laszlodaniel/ChryslerScanner/PCB/V142/Assemblies/OBD2_female_connector_01.STEP

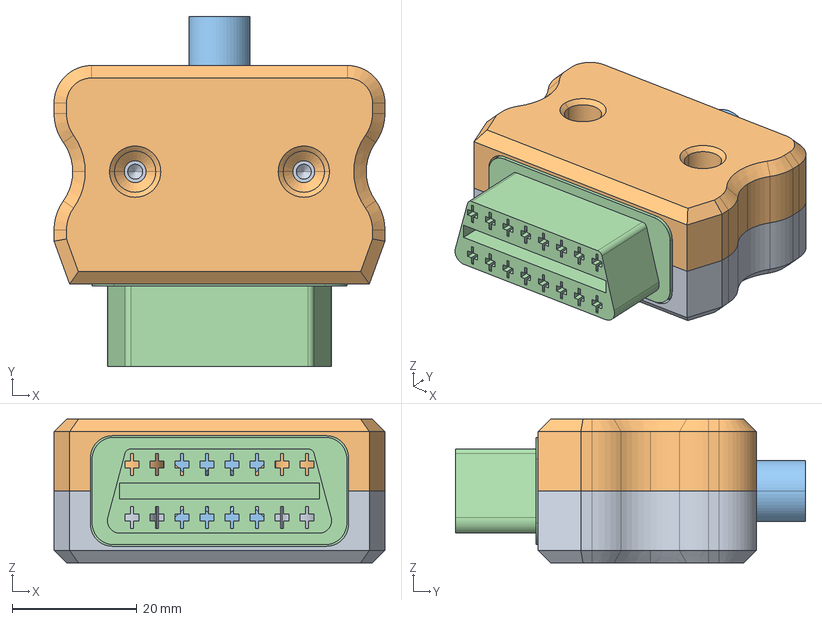
[picture p14: CAD file, 2019-10-13, an earlier design]
PCB/V142/Assemblies/OBD2_female_connector_01.STEP
53.0 x 56.1 x 23.0 mm
OBD2_connector_bottom_01
OBD2_connector_top_01
OBD2_cable_holder
SEP-A-OBD-D
