laszlodaniel/ChryslerScanner/PCB/V150/ChryslerCCDSCIScanner_V150/schematic/ChryslerCCDSCIScanner_V150_schematic_bw.pdf

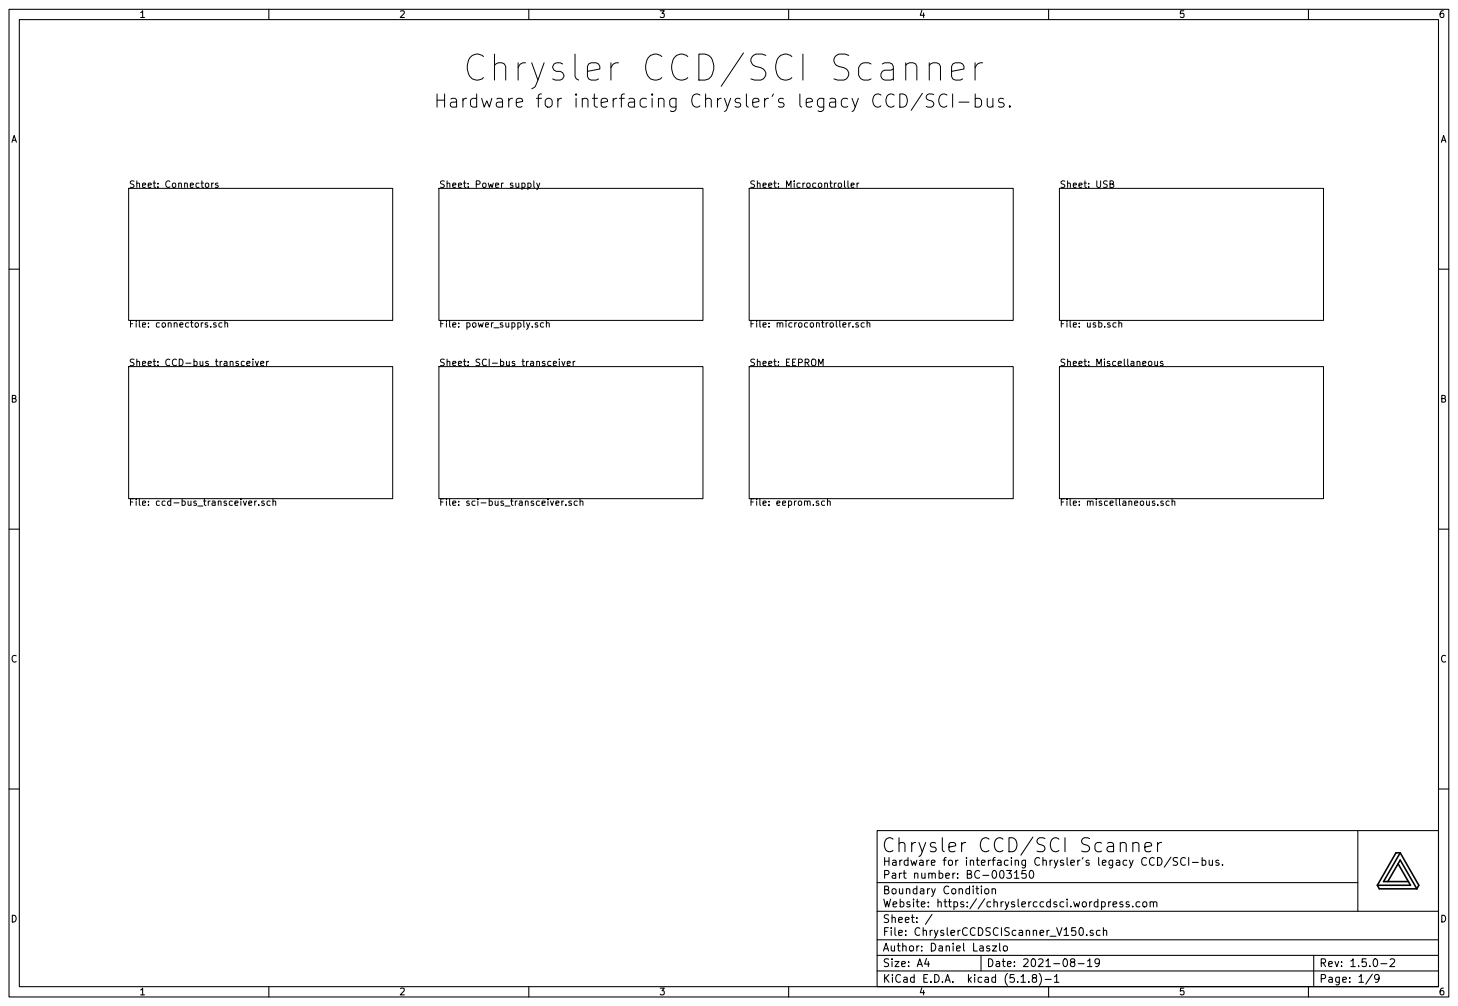
[picture p39: page 1]

Hardware for interfacing Chrysler's legacy CCD/SCI-bus.

Chrysler CCD/SCI Scanner
Part number: BC-003150 Hardware for interfacing Chrysler's legacy CCD/SCI-bus.

File: ChryslerCCDSCIScanner_V150.sch Sheet: / Boundary Condition Author: Daniel Laszlo Website: https://chryslerccdsci.wordpress.com

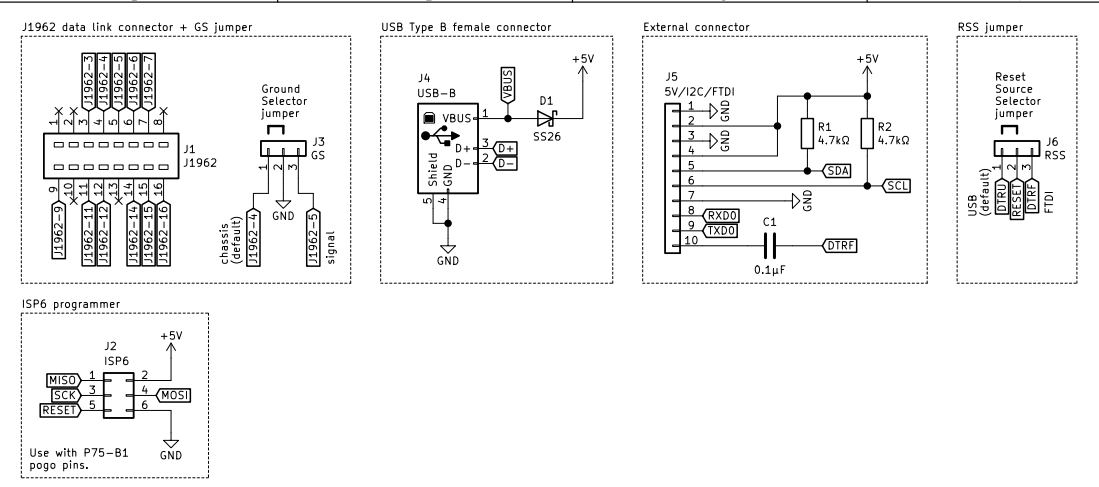
[picture p40: page 2]

Part number: BC-003150 Hardware for interfacing Chrysler's legacy CCD/SCI-bus. GND

Chrysler CCD/SCI Scanner File: connectors.sch Sheet: /Connectors/ Boundary Condition Author: Daniel Laszlo Website: https://chryslerccdsci.wordpress.com

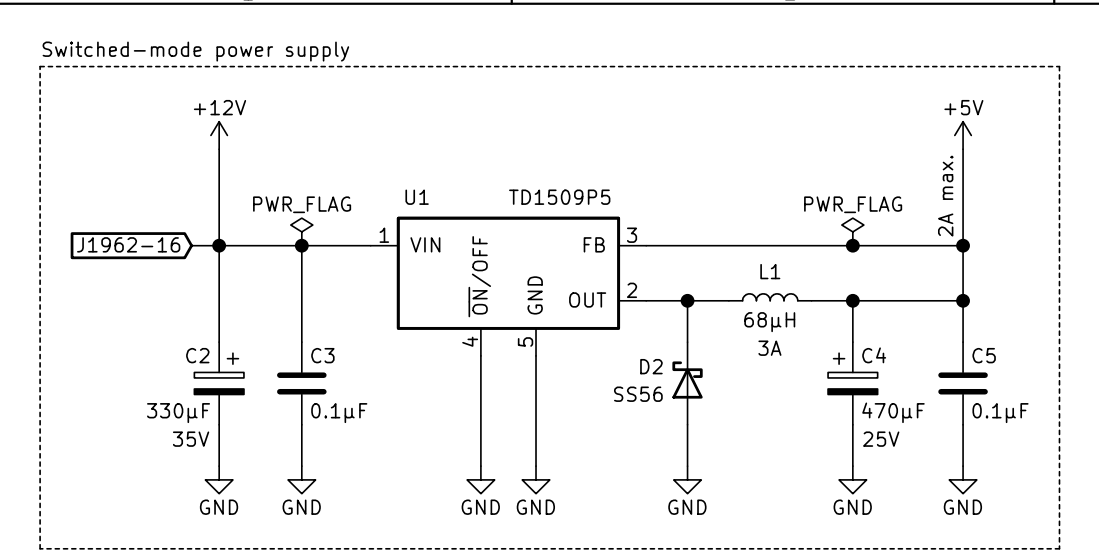
[picture p41: page 3]
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

Boundary Condition Author: Daniel Laszlo Website: https://chryslerccdsci.wordpress.com

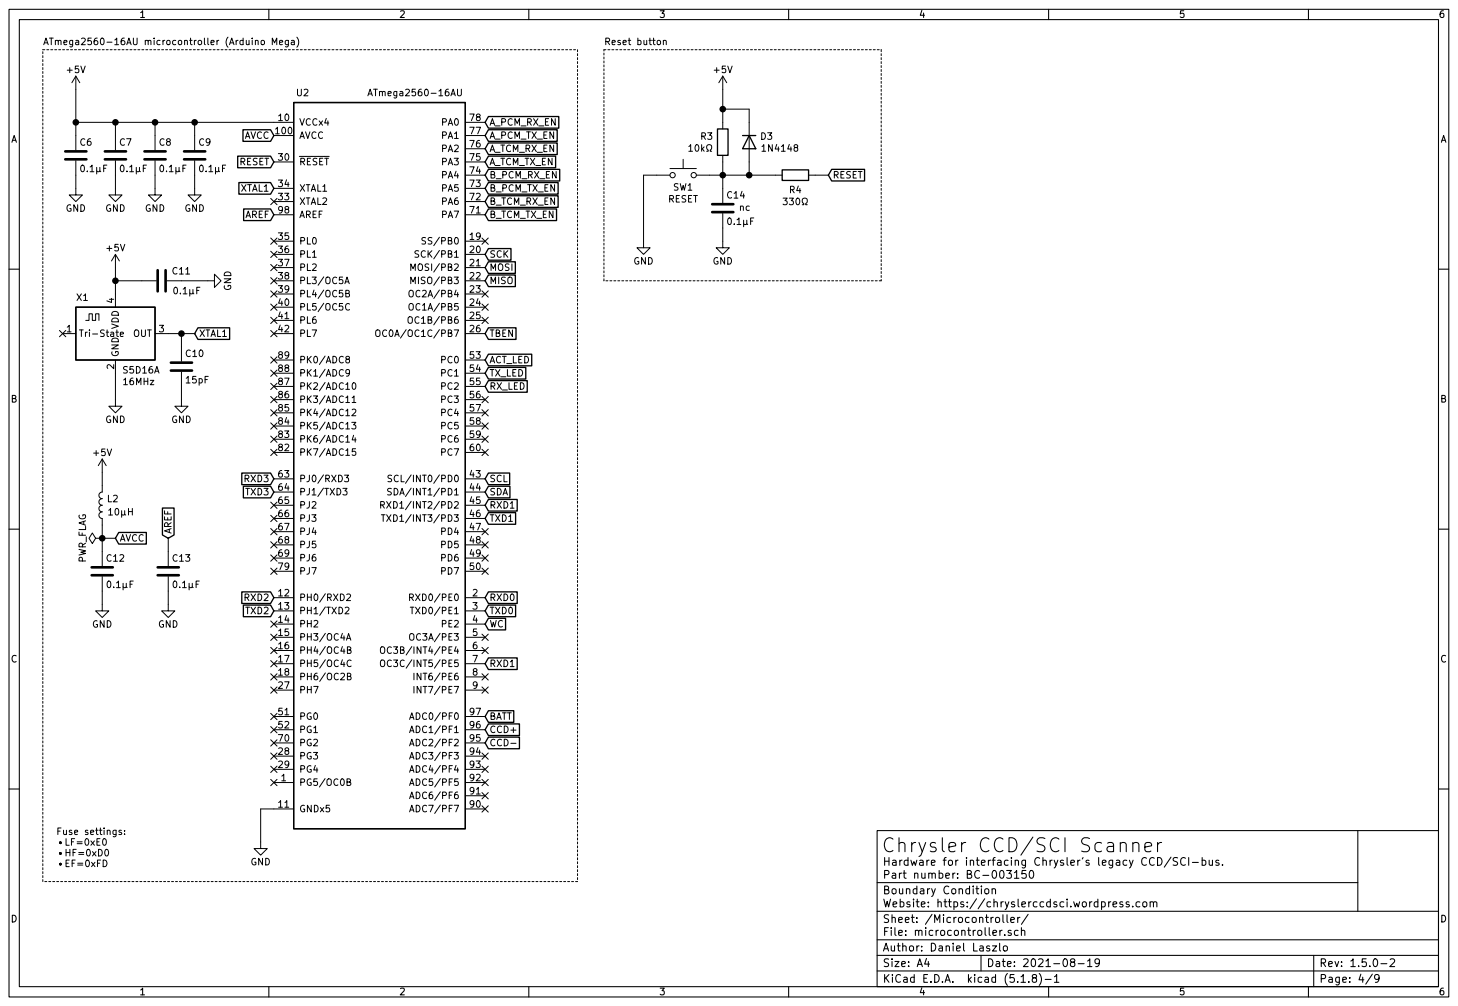
[picture p42: page 4]

Fuse settings: LF=0xE0 HF=0xD0 EF=0xFD

Chrysler CCD/SCI Scanner File: microcontroller.sch Sheet: /Microcontroller/ Boundary Condition Author: Daniel Laszlo Website: https://chryslerccdsci.wordpress.com

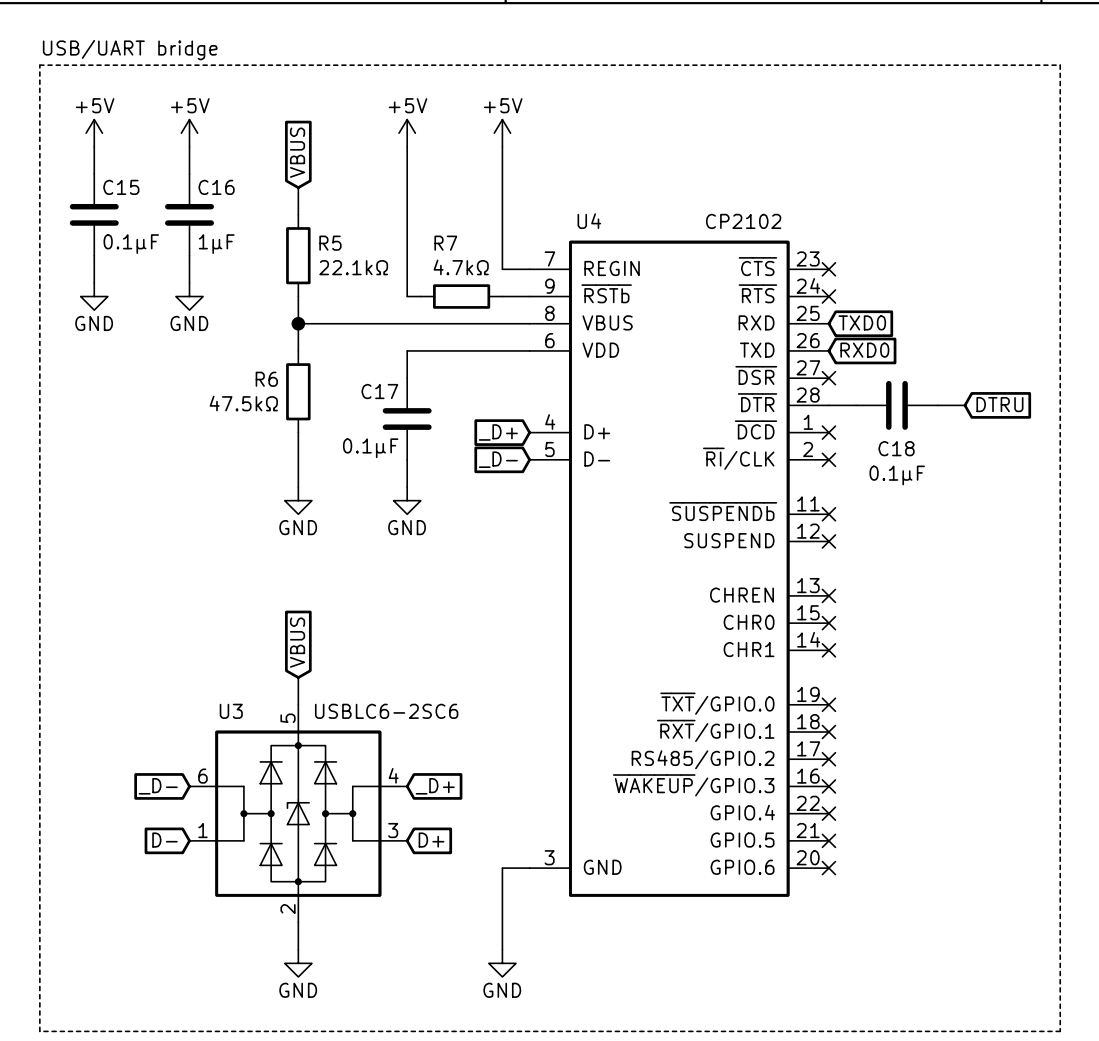
[picture p43: page 5]

Chrysler CCD/SCI Scanner File: usb.sch Sheet: /USB/ Boundary Condition Author: Daniel Laszlo Website: https://chryslerccdsci.wordpress.com
Part number: BC-003150 Hardware for interfacing Chrysler's legacy CCD/SCI-bus.

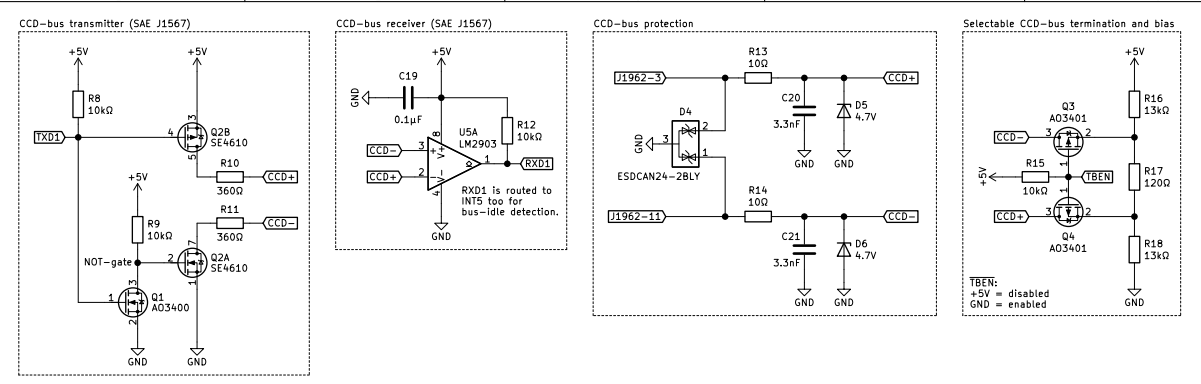
[picture p44: page 6]
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

File: ccd-bus_transceiver.sch Sheet: /CCD-bus transceiver/ Boundary Condition Author: Daniel Laszlo Website: https://chryslerccdsci.wordpress.com

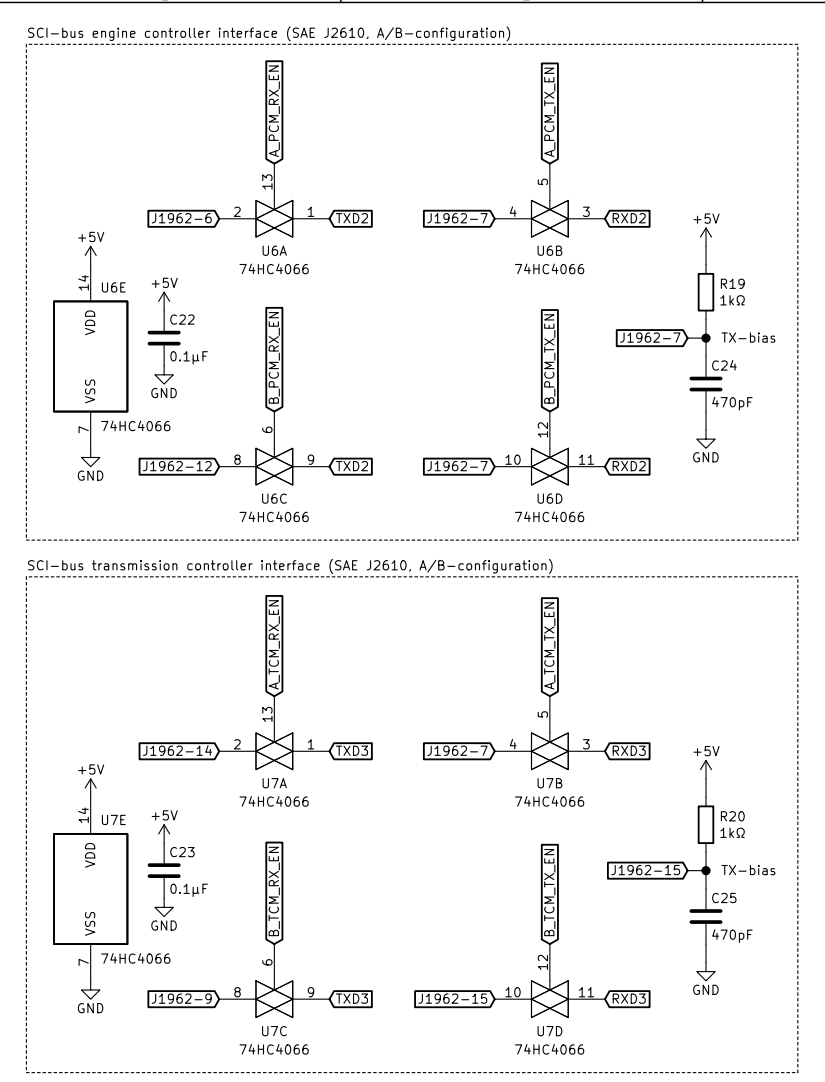
[picture p45: page 7]

Chrysler CCD/SCI Scanner

File: sci-bus_transceiver.sch Sheet: /SCI-bus transceiver/ Boundary Condition Author: Daniel Laszlo Website: https://chryslerccdsci.wordpress.com

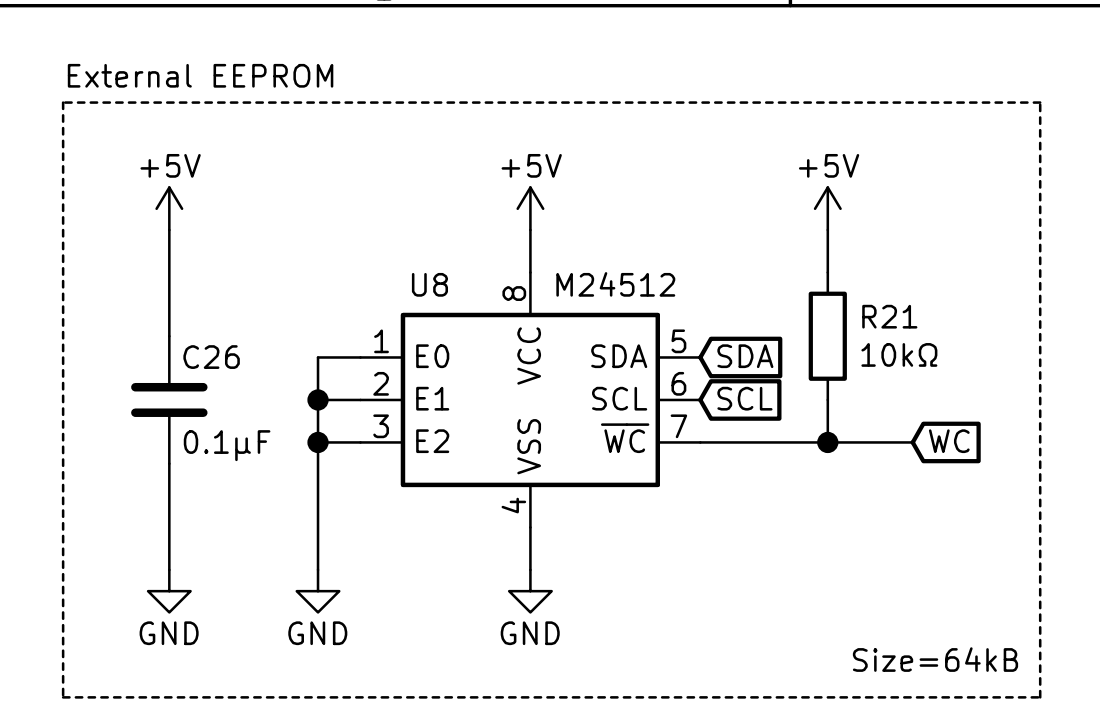
[picture p46: page 8]

4 SDA 5 SCL 6 WC 7 VCC

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

File: eeprom.sch Sheet: /EEPROM/ Boundary Condition Author: Daniel Laszlo Website: https://chryslerccdsci.wordpress.com

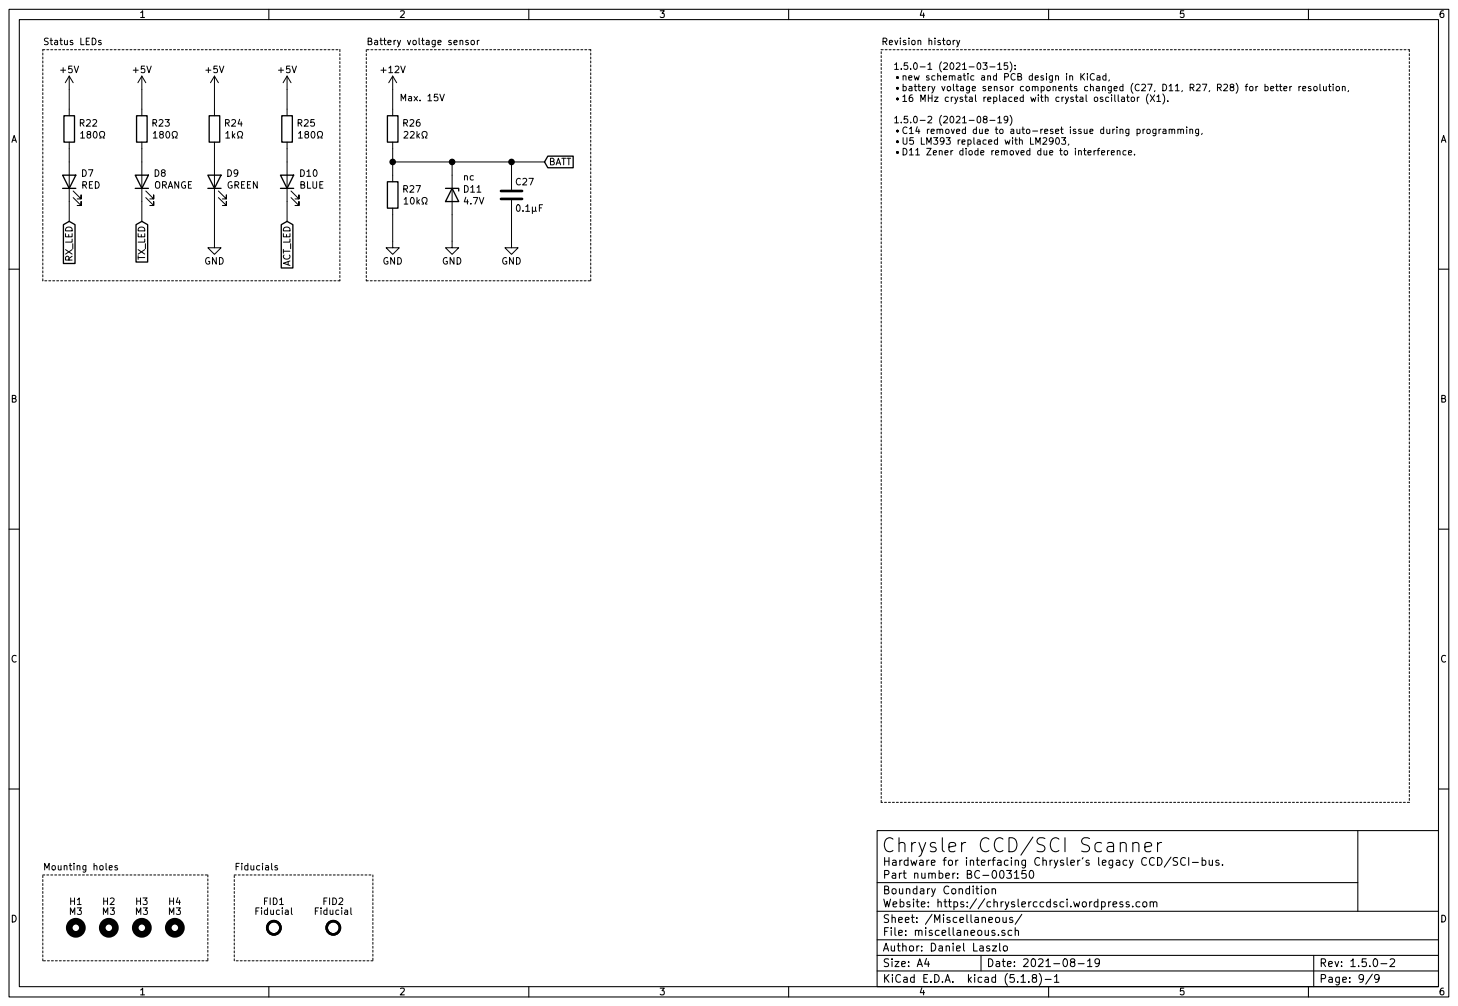
[picture p47: page 9]

new schematic and PCB design in KiCad,
battery voltage sensor components changed (C27, D11, R27, R28) for better resolution,
16 MHz crystal replaced with crystal oscillator (X1).

U5 LM393 replaced with LM2903, D11 Zener diode removed due to interference. Max. 15V Mounting holes

C14 removed due to auto-reset issue during programming,

Chrysler CCD/SCI Scanner File: miscellaneous.sch Sheet: /Miscellaneous/ Boundary Condition Author: Daniel Laszlo Website: https://chryslerccdsci.wordpress.com
Part number: BC-003150 Hardware for interfacing Chrysler's legacy CCD/SCI-bus.
