laszlodaniel/ChryslerScanner/PCB/V142/SCIBusLogicInverter_V100/schematic/SCIBusLogicInverter_V100_schematic.pdf

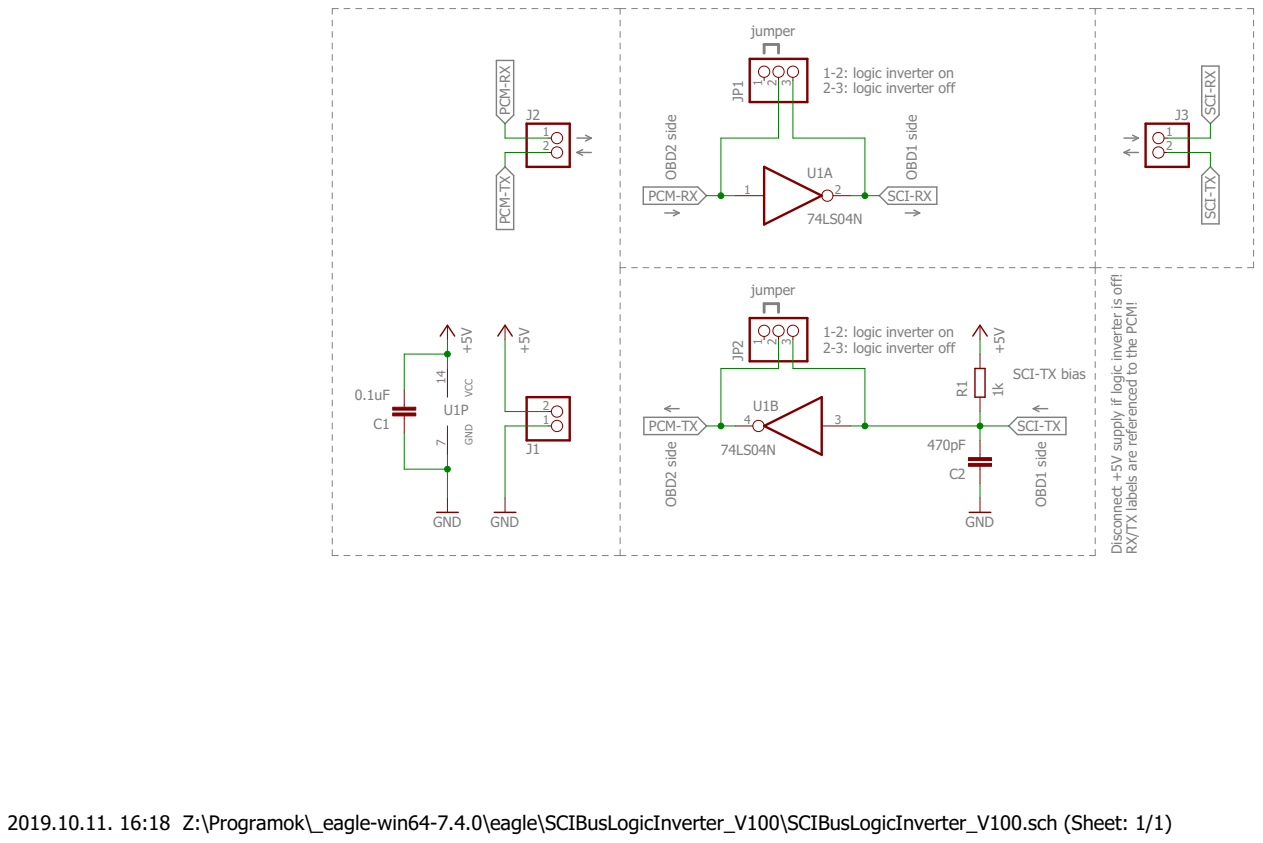
[picture p49: page 1]

SCI-TX SCI-RX

Disconnect +5V supply if logic inverter is of ! RX/TX labels are referenced to the PCM!

SCI-TX bias 1-2: logic inverter on
2-3: logic inverter off

2019.10.11. 16:18 Z:\Programok\_eagle-win64-7.4.0\eagle\SCIBusLogicInverter_V100\SCIBusLogicInverter_V100.sch (Sheet: 1/1)
