laszlodaniel/ChryslerScanner/PCB/V142/EngineConnector_V100/schematic/EngineConnector_V100_schematic.pdf

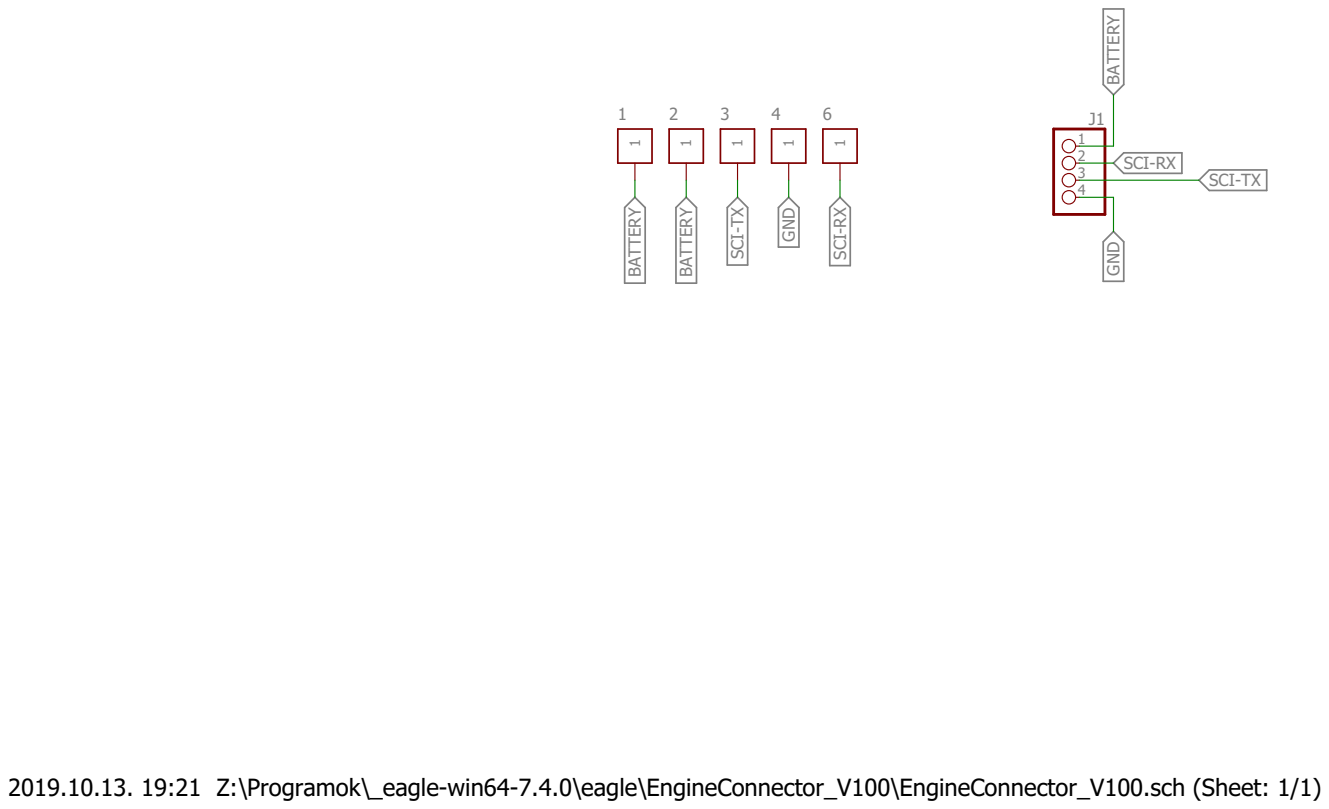
[picture p50: page 1]

2019.10.13. 19:21 Z:\Programok\_eagle-win64-7.4.0\eagle\EngineConnector_V100\EngineConnector_V100.sch (Sheet: 1/1)
