laszlodaniel/ChryslerScanner/Arduino/ChryslerCCDSCIScanner/ChryslerCCDSCIScanner.ino

/*
 * ChryslerCCDSCIScanner (https://github.com/laszlodaniel/ChryslerCCDSCIScanner)
 * Copyright (C) 2018-2023 Daniel Laszlo
 *
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
 * UART code is based on original library by Andy Gock:
 * https://github.com/andygock/avr-uart
 *
 * Board: Arduino/Genuino Mega or Mega 2560
 * Processor: ATmega2560 (Mega 2560)
 */

#include <avr/boot.h>
#include <avr/eeprom.h>
#include <avr/interrupt.h>
#include <avr/io.h>
#include <avr/pgmspace.h>
#include <avr/wdt.h>
#include <util/atomic.h>
#include <EEPROM.h>
#include <LiquidCrystal_I2C.h> // https://github.com/fdebrabander/Arduino-LiquidCrystal-I2C-library
#include <Wire.h>
#include <extEEPROM.h> // https://github.com/JChristensen/extEEPROM
#include <CCDLibrary.h> // https://github.com/laszlodaniel/CCDLibrary

// Firmware version (hexadecimal format):
// 00: major
// 09: minor
// 0C: patch
// (00: revision)
// = v0.9.12(.0)
#define FW_VERSION 0x00090C00

// Firmware date/time of compilation in 32-bit UNIX time:
// https://www.epochconverter.com/hex
// Upper 32 bits contain the firmware version.
#define FW_DATE 0x00090C006697BBA8

// Set (1), clear (0) and invert (1->0; 0->1) bit in a register or variable easily
//#define sbi(variable, bit) (variable) |=  (1 << (bit))
//#define cbi(variable, bit) (variable) &= ~(1 << (bit))
//#define ibi(variable, bit) (variable) ^=  (1 << (bit))

#define to_uint16(hb, lb)           (uint16_t)(((uint8_t)hb << 8) | (uint8_t)lb)
#define to_uint32(msb, hb, lb, lsb) (uint32_t)(((uint32_t)msb << 24) | ((uint32_t)hb << 16) | ((uint32_t)lb << 8) | (uint32_t)lsb)
#define ARRAY_SIZE(A) (sizeof(A) / sizeof((A)[0]))

#define USB_RX_BUFFER_SIZE 1024
#define USB_TX_BUFFER_SIZE 1024
#define USB_RX_BUFFER_MASK (USB_RX_BUFFER_SIZE - 1)
#define USB_TX_BUFFER_MASK (USB_TX_BUFFER_SIZE - 1)

#define USB_RECEIVE_INTERRUPT  USART0_RX_vect
#define USB_TRANSMIT_INTERRUPT USART0_UDRE_vect
#define USB_STATUS             UCSR0A
#define USB_CONTROL            UCSR0B
#define USB_DATA               UDR0
#define USB_UDRIE              UDRIE0

#define PCM_RX_BUFFER_SIZE 256
#define PCM_TX_BUFFER_SIZE 256
#define PCM_RX_BUFFER_MASK (PCM_RX_BUFFER_SIZE - 1)
#define PCM_TX_BUFFER_MASK (PCM_TX_BUFFER_SIZE - 1)

#define PCM_RECEIVE_INTERRUPT  USART2_RX_vect
#define PCM_TRANSMIT_INTERRUPT USART2_UDRE_vect
#define PCM_STATUS             UCSR2A
#define PCM_CONTROL            UCSR2B
#define PCM_DATA               UDR2
#define PCM_UDRIE              UDRIE2  

#define TCM_RX_BUFFER_SIZE 256
#define TCM_TX_BUFFER_SIZE 256
#define TCM_RX_BUFFER_MASK (TCM_RX_BUFFER_SIZE - 1)
#define TCM_TX_BUFFER_MASK (TCM_TX_BUFFER_SIZE - 1)

#define TCM_RECEIVE_INTERRUPT  USART3_RX_vect
#define TCM_TRANSMIT_INTERRUPT USART3_UDRE_vect
#define TCM_STATUS             UCSR3A
#define TCM_CONTROL            UCSR3B
#define TCM_DATA               UDR3
#define TCM_UDRIE              UDRIE3

#define BATT         A0 // battery voltage sensor analog input
#define CCD_POSITIVE A1 // CCD+ analog input
#define CCD_NEGATIVE A2 // CCD- analog input
#define TBEN         13 // CCD-bus termination and bias enable pin

#define A_PCM_RX_EN 22 // SCI-bus configuration selector digital pins on ATmega2560
#define A_PCM_TX_EN 23
#define A_TCM_RX_EN 24
#define A_TCM_TX_EN 25
#define B_PCM_RX_EN 26
#define B_PCM_TX_EN 27
#define B_TCM_RX_EN 28
#define B_TCM_TX_EN 29

#define RX_LED  35 // status LED (red), message received
#define TX_LED  36 // status LED (orange), message sent
#define ACT_LED 37 // status LED (blue), activity

// SAE J2610 (SCI-bus) recommended delays in milliseconds
#define SCI_LS_T1_DELAY 20
#define SCI_LS_T2_DELAY 100
#define SCI_LS_T3_DELAY 50
#define SCI_LS_T4_DELAY 20
#define SCI_LS_T5_DELAY 100
#define SCI_HS_T1_DELAY 1
#define SCI_HS_T2_DELAY 1
#define SCI_HS_T3_DELAY 5
#define SCI_HS_T4_DELAY 0
#define SCI_HS_T5_DELAY 0
#define SCI_BTSTRP_DLY  20

// SCI-bus setting bits
#define SCI_STATE_BIT         7
#define SCI_SBEC2_BIT         6
#define SCI_MODULE_BIT        5
#define SCI_NGC_BIT           4
#define SCI_LOGIC_BIT         3
#define SCI_CONFIG_BIT        2
#define SCI_SPEED_BITS        3
#define SCI_SPEED_BAUD_976    0
#define SCI_SPEED_BAUD_7812   1
#define SCI_SPEED_BAUD_62500  2
#define SCI_SPEED_BAUD_125000 3

// CCD-bus setting bits
#define CCD_STATE_BIT         7
#define CCD_TBEN_BIT          6

//#define UART_FRAME_ERROR        0x1000  /**< Framing Error by UART          00010000 00000000 - FIXED BIT */ 
//#define UART_OVERRUN_ERROR      0x0800  /**< Overrun condition by UART      00001000 00000000 - FIXED BIT */
//#define UART_BUFFER_OVERFLOW    0x0400  /**< Receive ringbuffer overflow    00000100 00000000 - ARBITRARY */
#define UART_RX_NO_DATA         0x0200  /**< Receive buffer is empty        00000010 00000000 - ARBITRARY */

// Baudrate prescaler calculation: UBRR = (F_CPU / (16 * BAUDRATE)) - 1
#define BAUD_976    1023 // prescaler for  976.5 baud speed (SCI-bus extra-low speed)
#define BAUD_7812   127  // prescaler for 7812.5 baud speed (CCD/SCI-bus default low-speed diagnostic mode)
#define BAUD_62500  15   // prescaler for  62500 baud speed (SCI-bus high-speed parameter mode)
#define BAUD_125000 7    // prescaler for 125000 baud speed (SCI-bus extra-high speed)
#define BAUD_250000 3    // prescaler for 250000 baud speed (USB communication)

#define PACKET_SYNC_BYTE   0x3D // "=" symbol
#define ASCII_SYNC_BYTE    0x3E // ">" symbol
#define MAX_PAYLOAD_LENGTH USB_RX_BUFFER_SIZE - 6  // 1024-6 bytes
#define EMPTY_PAYLOAD      0xFE  // Random byte, could be anything

#define BUFFER_SIZE 256

// DATA CODE byte building blocks
// Bus masks (high nibble (3 bits))
#define bus_usb             0x00 // when sending packets back to laptop use "from_" masks to specify source
#define bus_ccd             0x01
#define bus_pcm             0x02
#define bus_tcm             0x03
// Commands (low nibble (4 bits))
#define reset               0x00
#define handshake           0x01
#define status              0x02
#define settings            0x03
#define request             0x04
#define response            0x05
#define msg_tx              0x06
#define msg_rx              0x07
// 0x08-0x0D reserved
#define debug               0x0E
#define ok_error            0x0F

// SUB-DATA CODE byte
// Command 0x00 (reset)
#define reset_in_progress   0x00
#define reset_done          0x01
// 0x02-0xFF reserved

// SUB-DATA CODE byte
// Command 0x01 (handshake)
// 0x00-0xFF reserved

// SUB-DATA CODE byte
// Command 0x02 (status)
// 0x00-0xFF reserved

// SUB-DATA CODE byte
// Command 0x03 (settings)
#define heartbeat           0x01 // ACT_LED flashing interval is stored in payload
#define set_ccd_bus         0x02 // ON-OFF state is stored in payload
#define set_sci_bus         0x03 // ON-OFF state, A/B configuration and speed are stored in payload
#define set_repeat_behavior 0x04 // Repeated message behavior settings
#define set_lcd             0x05 // ON-OFF state
// 0x06-0xFF reserved 

// SUB-DATA CODE byte
// Command 0x04 & 0x05 (request and response)
#define hwfw_info           0x01 // Hardware version/date and firmware date in this particular order (dates are in 64-bit UNIX time format)
#define timestamp           0x02 // elapsed milliseconds since system start
#define battery_voltage     0x03 // flag for battery voltage packet
#define exteeprom_checksum  0x04
#define ccd_bus_voltages    0x05
// 0x06-0xFF reserved

// SUB-DATA CODE byte
// Command 0x06 (msg_tx)
#define stop_msg_flow       0x01 // stop message transmission (single and repeated as well)         
#define single_msg          0x02 // send message to the target bus specified in DATA CODE byte; message is stored in payload 
#define list_msg            0x03 // send a set of messages to the target bus specified in DATA CODE byte; messages are stored in payload
#define repeated_single_msg 0x04 // send message(s) repeatedly to the target bus sepcified in DATA CODE byte
#define repeated_list_msg   0x05 // send a fixed set of messages repeatedly to the target bus specified in DATA CODE byte
// 0x06-0xFF reserved

// SUB-DATA CODE byte
// Command 0x07 (msg_rx)
#define sci_ls_bytes        0x01 // low-speed SCI-bus message
#define sci_hs_bytes        0x02 // high-speed SCI-bus message
// 0x03-0xFF reserved

// SUB-DATA CODE byte
// Command 0x0E (debug)
#define random_ccd_msg            0x01
#define read_inteeprom_byte       0x02
#define read_inteeprom_block      0x03
#define read_exteeprom_byte       0x04
#define read_exteeprom_block      0x05
#define write_inteeprom_byte      0x06
#define write_inteeprom_block     0x07
#define write_exteeprom_byte      0x08
#define write_exteeprom_block     0x09
#define set_arbitrary_uart_speed  0x0A
#define init_bootstrap_mode       0x0B
#define upload_worker_function    0x0C
#define start_worker_function     0x0D
#define exit_worker_function      0x0E
#define restore_pcm_eeprom        0xF0

// SUB-DATA CODE byte
// Command 0x0F (ok_error)
#define ok                                      0x00
#define error_length_invalid_value              0x01
#define error_datacode_invalid_command          0x02
#define error_subdatacode_invalid_value         0x03
#define error_payload_invalid_values            0x04
#define error_packet_checksum_invalid_value     0x05
#define error_packet_timeout_occurred           0x06
#define error_buffer_overflow                   0x07
#define error_datacode_invalid_bus              0x08
// 0x09-0xF6 reserved
#define error_sci_ls_no_response                0xF6
#define error_not_enough_mcu_ram                0xF7
#define error_sci_hs_memory_ptr_no_response     0xF8
#define error_sci_hs_invalid_memory_ptr         0xF9
#define error_sci_hs_no_response                0xFA
#define error_eep_not_found                     0xFB
#define error_eep_read                          0xFC
#define error_eep_write                         0xFD
#define error_internal                          0xFE
#define error_fatal                             0xFF

#define STOP  0x00
#define START 0x01

uint8_t ack[1] = { 0x00 }; // acknowledge payload array
uint8_t err[1] = { 0xFF }; // error payload array

uint8_t avr_signature[3];
uint8_t hw_version[2];
uint8_t hw_date[8];
uint8_t assembly_date[8];

uint32_t current_millis = 0;
uint8_t current_timestamp[4]; // current time is stored here when "update_timestamp" is called

uint8_t command_timeout = 100; // milliseconds
uint16_t command_purge_timeout = 200; // milliseconds, if a command isn't complete within this time then delete the usb receive buffer

typedef struct {
    bool enabled = false; // bus state (enabled or disabled)
    bool termination_bias_enabled = false;
    bool inverted_logic = false; // OBD1 SCI engine adapter cable needs special message handling
    bool sbec2_mode = false; // OBD1 reverse bit order inside byte
    bool ngc_mode = false; // NGC computers use full-duplex SCI-bus communication
    uint8_t bus_settings = 0;
    uint16_t speed = BAUD_7812; // baudrate prescaler - 1023: 976.5625 baud; 127: 7812.5 baud; 15: 62500 baud; 7: 125000 baud; 3: 250000 baud
    volatile bool idle = true; // bus idling (CCD-bus only, IDLE-pin)
    volatile bool busy = false; // there's a byte being transmitted on the bus (CCD-bus only, CTRL-pin)
    bool echo_received = false; // low-speed mode (7812.5 baud)
    bool response_received = false; // low-speed mode (7812.5 baud) typical 1-byte response flag
    uint8_t message[32];
    uint16_t message_length = 0;
    uint8_t msg_buffer[BUFFER_SIZE]; // temporary buffer to store outgoing or current repeated messages
    uint16_t msg_buffer_ptr = 0; // message length in the buffer, this points to the first empty slot after the last byte
    uint8_t msg_to_transmit_count = 0;
    uint8_t msg_to_transmit_count_ptr = 0;
    volatile uint32_t last_byte_millis = 0;
    bool msg_tx_pending = false; // message is awaiting to be transmitted to the bus
    bool repeat = false;
    bool repeat_next = false;
    bool repeat_list_once = false;
    bool repeat_stop = true;
    uint16_t repeated_msg_length = 0;
    uint32_t repeated_msg_raw_start = 0; // iteration start, 4-bytes max
    uint32_t repeated_msg_raw_end = 0; // iteration end, 4-bytes max
    uint16_t repeated_msg_increment = 1; // if iteration is true then the counter in the message will increase this much for every new message
    uint16_t repeated_msg_interval = 100; // ms
    uint32_t repeated_msg_last_millis = 0;
    uint8_t repeat_retry_counter = 0;
    bool random_msg = false;
    uint16_t random_msg_interval = 0;
    uint16_t random_msg_interval_min = 0;
    uint16_t random_msg_interval_max = 0;
    uint32_t random_msg_last_millis = 0;
    volatile uint32_t msg_rx_count = 0; // total received messages
    volatile uint32_t msg_tx_count = 0; // total transmitted messages
    uint8_t last_hs_memarea = 0xF4;
    uint8_t auto_request = 0;
} bus_t;

bus_t ccd, pcm, tcm;

// Construct an object called "eep" for the external 24LC32A EEPROM chip.
extEEPROM eep(kbits_32, 1, 32, 0x50); // device size: 32 kilobits = 4 kilobytes, number of devices: 1, page size: 32 bytes (from datasheet), device address: 0x50 by default

bool eep_present = false;
uint8_t eep_status = 0; // extEEPROM connection status is stored here
uint8_t eep_result = 0; // extEEPROM 

// Construct an object called "lcd" for the external display.
LiquidCrystal_I2C lcd(0x27, 20, 4);

bool lcd_enabled = false;
uint8_t lcd_i2c_address = 0;
uint8_t lcd_char_width = 0;
uint8_t lcd_char_height = 0;
uint8_t lcd_refresh_rate = 0;
uint8_t lcd_units = 0; // 0-imperial, 1-metric
uint8_t lcd_data_source = 1; // 1: CCD-bus, 2: SCI-bus (PCM), 3: SCI-bus (TCM)
uint32_t lcd_last_update = 0;
uint16_t lcd_update_interval = 0;
bool lcd_splash_screen_on = true;

// Custom LCD-characters
// https://maxpromer.github.io/LCD-Character-Creator/
uint8_t up_symbol[8]     = { 0x00, 0x04, 0x0E, 0x15, 0x04, 0x04, 0x00, 0x00 }; // ↑
uint8_t down_symbol[8]   = { 0x00, 0x04, 0x04, 0x15, 0x0E, 0x04, 0x00, 0x00 }; // ↓
uint8_t left_symbol[8]   = { 0x00, 0x04, 0x08, 0x1F, 0x08, 0x04, 0x00, 0x00 }; // ←
uint8_t right_symbol[8]  = { 0x00, 0x04, 0x02, 0x1F, 0x02, 0x04, 0x00, 0x00 }; // →
uint8_t enter_symbol[8]  = { 0x00, 0x01, 0x05, 0x09, 0x1F, 0x08, 0x04, 0x00 }; // 
uint8_t degree_symbol[8] = { 0x06, 0x09, 0x09, 0x06, 0x00, 0x00, 0x00, 0x00 }; // °

char vin_characters[] = "-----------------"; // 17 characters
String vin_string;

volatile uint8_t  USB_RxBuf[USB_RX_BUFFER_SIZE];
volatile uint8_t  USB_TxBuf[USB_TX_BUFFER_SIZE];
volatile uint16_t USB_RxHead; // since buffer size is bigger than 256 bytes it has to be a 16-bit (int) variable
volatile uint16_t USB_RxTail;
volatile uint16_t USB_TxHead;
volatile uint16_t USB_TxTail;
volatile uint8_t  USB_LastRxError;

volatile uint8_t PCM_RxBuf[PCM_RX_BUFFER_SIZE];
volatile uint8_t PCM_TxBuf[PCM_TX_BUFFER_SIZE];
volatile uint8_t PCM_RxHead;
volatile uint8_t PCM_RxTail;
volatile uint8_t PCM_TxHead;
volatile uint8_t PCM_TxTail;
volatile uint8_t PCM_LastRxError;

volatile uint8_t TCM_RxBuf[TCM_RX_BUFFER_SIZE];
volatile uint8_t TCM_TxBuf[TCM_TX_BUFFER_SIZE];
volatile uint8_t TCM_RxHead;
volatile uint8_t TCM_RxTail;
volatile uint8_t TCM_TxHead;
volatile uint8_t TCM_TxTail;
volatile uint8_t TCM_LastRxError;

uint8_t sci_hi_speed_memarea[16] = { 0xF0, 0xF1, 0xF2, 0xF3, 0xF4, 0xF5, 0xF6, 0xF7, 0xF8, 0xF9, 0xFA, 0xFB, 0xFC, 0xFD, 0xFE, 0xFF };
uint8_t sci_lo_speed_cmd_filter[6] = { 0x14, 0x15, 0x26, 0x27, 0x28, 0x2A };

uint32_t ccd_positive_adc = 0;   // raw analog reading is stored here
uint16_t ccd_positive_volts = 0; // converted to CCD+ voltage and multiplied by 100: 2.51V -> 251
uint32_t ccd_negative_adc = 0;   // raw analog reading is stored here
uint16_t ccd_negative_volts = 0; // converted to CCD- voltage and multiplied by 100: 2.51V -> 251
uint8_t ccd_volts_array[4]; // ccd_positive_volts and ccd_negative_volts is separated to byte components here

uint32_t previous_random_ccd_msg_millis = 0;

uint16_t adc_supply_voltage = 500; // supply voltage multiplied by 100: 5.00V -> 500
uint16_t rd_high_value = 27000; // high resistor value in the divider (R19): 27 kOhm = 27000
uint16_t rd_low_value = 5000;  // low resistor value in the divider (R20): 5 kOhm = 5000
uint16_t adc_max_value = 1023; // 1023 for 10-bit resolution
uint32_t battery_adc = 0;   // raw analog reading is stored here
uint16_t battery_volts = 0; // converted to battery voltage and multiplied by 100: 12.85V -> 1285
uint8_t battery_volts_array[2]; // battery_volts is separated to byte components here
bool connected_to_vehicle = false;

uint32_t rx_led_ontime = 0;
uint32_t tx_led_ontime = 0;
uint32_t act_led_ontime = 0;
uint32_t previous_act_blink = 0;
uint16_t led_blink_duration = 50; // milliseconds
uint16_t heartbeat_interval = 5000; // milliseconds
bool heartbeat_enabled = true;

// Bootloaders:

// SBEC3 (128k).
const uint8_t LdBoot_128k_SBEC3[516] PROGMEM =
{
    0x37, 0x80, 0x00, 0xac, 0xfa, 0x00, 0x01, 0x98, 0xf8, 0x10, 0xb7, 0x02, 0xf8, 0x20, 0xb7, 0x58, 
    0xb6, 0xee, 0xf5, 0x11, 0xfa, 0x00, 0x01, 0x82, 0xfa, 0x00, 0x01, 0x98, 0x17, 0xfa, 0x01, 0xb0, 
    0x17, 0xf5, 0x01, 0xb0, 0xfa, 0x00, 0x01, 0x82, 0xfa, 0x00, 0x01, 0x98, 0x17, 0xfa, 0x01, 0xb1, 
    0x17, 0xf5, 0x01, 0xb1, 0xfa, 0x00, 0x01, 0x82, 0xf5, 0x00, 0x37, 0x9c, 0x37, 0xbc, 0x02, 0x00, 
    0xfa, 0x00, 0x01, 0x98, 0xca, 0x00, 0xc5, 0x00, 0xfa, 0x00, 0x01, 0x82, 0x3c, 0x01, 0x27, 0x31, 
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
    0x37, 0xfc, 0xf5, 0xa5, 0x27, 0xf7, 0x17, 0x65, 0x7c, 0x0c, 0x76, 0x01, 0xb7, 0xf4, 0x17, 0xea, 
    0x7c, 0x0f, 0x27, 0xf7, 0x17, 0x65, 0x7c, 0x0d, 0x76, 0x42, 0x78, 0x40, 0xb6, 0xf2, 0x17, 0xe5, 
    0x7c, 0x0f, 0x27, 0xf7, 0x37, 0xb0, 0x00, 0x01, 0xb6, 0xf6, 0x27, 0xf7, 0x27, 0x4c, 0x27, 0x4c, 
    0x27, 0x4c, 0x27, 0x4c
};

// Empty.
const uint8_t LdWorker_empty_SBEC3[2] =
{
    0x27, 0xf7
};

/*************************************************************************
Function: solve_sbec3_bootstrap_seed()
Purpose:  solve the bootstrap security challenge
Note:     provided by Konstantin aka Piton
**************************************************************************/
uint16_t solve_sbec3_bootstrap_seed(uint16_t input)
{
    uint16_t seed = (input + 0x247C) | 5;
    int i = seed & 0x0F;

    while (i--)
    {
        if (seed & 1) seed = ((seed >> 1) | 0x8000);
        else seed >>= 1;
    }

    return (seed | 0x247C);
}

uint16_t pcm_peek(uint16_t index = 0); // function prototype

/*************************************************************************
Function: unlock_bootstrap_mode()
Purpose:  solve the bootstrap security seed and upload bootloader
**************************************************************************/
void unlock_sbec3_bootstrap_mode(uint8_t bootloader_src)
{
    uint8_t ret[1] = { 0 };
    // 0 = ok
    // 1 = no response to magic byte
    // 2 = unexpected response to magic byte
    // 3 = security seed response timeout
    // 4 = security seed response checksum error
    // 5 = security key status timeout
    // 6 = security key not accepted
    // 7 = start bootloader timeout
    // 8 = unexpected bootloader status byte

    uint8_t buff[16];
    uint8_t checksum = 0;
    bool key_required = true;

    wdt_reset(); // feed the watchdog
    pcm_rx_flush();
    pcm_tx_flush();
    pcm.last_byte_millis = millis();

    // Write magic byte to set 62500 baud.
    pcm_putc(0x7F);

    while ((uint32_t)(millis() - pcm.last_byte_millis) < SCI_BTSTRP_DLY); // wait for response

    if (pcm_rx_available() == 0)
    {
        ret[0] = 1;
        send_usb_packet(bus_usb, debug, init_bootstrap_mode, ret, 1);
        pcm_rx_flush();
        return;
    }

    buff[0] = pcm_getc() & 0xFF;

    if (buff[0] != 0x06)
    {
        ret[0] = 2;
        send_usb_packet(bus_usb, debug, init_bootstrap_mode, ret, 1);
        pcm_rx_flush();
        return;
    }

    uint8_t req_seed_cmd[5] = { 0x24, 0xD0, 0x27, 0xC1, 0xDC };

    wdt_reset(); // feed the watchdog
    pcm_rx_flush();
    pcm.last_byte_millis = millis();

    // Write security seed request message.
    for (uint8_t i = 0; i < ARRAY_SIZE(req_seed_cmd); i++)
    {
        pcm_putc(req_seed_cmd[i]);
    }

    while ((uint32_t)(millis() - pcm.last_byte_millis) < (2 * SCI_BTSTRP_DLY)); // wait for response

    if (pcm_rx_available() < 7)
    {
        if ((pcm_rx_available() == 5) && (pcm_peek(0) == 0xDB) && (pcm_peek(1) == 0x2F) && (pcm_peek(2) == 0xD8) && (pcm_peek(3) == 0x3E) && (pcm_peek(4) == 0x23))
        {
            key_required = false;
        }
        else
        {
            ret[0] = 3;
            send_usb_packet(bus_usb, debug, init_bootstrap_mode, ret, 1);
            pcm_rx_flush();
            return;
        }
    }

    if (key_required)
    {
        // Read security seed response.
        for (uint8_t i = 0; i < 7; i++)
        {
            buff[i] = pcm_getc() & 0xFF;
    
            if (i < 6) checksum += buff[i]; // calculate checksum
        }

        uint8_t key[2];

        // Evaluate seed response message and solve the puzzle.
        if ((buff[0] == 0x26) && (buff[1] == 0xD0) && (buff[2] == 0x67) && (buff[3] == 0xC1) && (buff[6] == checksum))
        {
            uint16_t data = solve_sbec3_bootstrap_seed(to_uint16(buff[4], buff[5]));
            key[0] = (data >> 8) & 0xFF;
            key[1] = data & 0xFF;
        }
        else
        {
            ret[0] = 4;
            send_usb_packet(bus_usb, debug, init_bootstrap_mode, ret, 1);
            pcm_rx_flush();
            return;
        }

        uint8_t send_key_cmd[7] = { 0x24, 0xD0, 0x27, 0xC2, key[0], key[1], 0 };
        send_key_cmd[6] = calculate_checksum(send_key_cmd, 0, ARRAY_SIZE(send_key_cmd) - 1);

        wdt_reset(); // feed the watchdog
        pcm_rx_flush();
        pcm.last_byte_millis = millis();

        // Write security key message.
        for (uint8_t i = 0; i < ARRAY_SIZE(send_key_cmd); i++)
        {
            pcm_putc(send_key_cmd[i]);
        }

        while ((uint32_t)(millis() - pcm.last_byte_millis) < (2 * SCI_BTSTRP_DLY)); // wait for response

        if (pcm_rx_available() < 5)
        {
            ret[0] = 5;
            send_usb_packet(bus_usb, debug, init_bootstrap_mode, ret, 1);
            pcm_rx_flush();
            return;
        }

        // Read security key status.
        for (uint8_t i = 0; i < 5; i++)
        {
            buff[i] = pcm_getc() & 0xFF;
        }

        // Key not accepted.
        if (!((buff[0] == 0x26) && (buff[1] == 0xD0) && (buff[2] == 0x67) && (buff[3] == 0xC2) && (buff[4] == 0x1F)))
        {
            ret[0] = 6;
            send_usb_packet(bus_usb, debug, init_bootstrap_mode, ret, 1);
            pcm_rx_flush();
            return;
        }
    }

    wdt_reset(); // feed the watchdog
    pcm_rx_flush();

    // Upload bootloader.
    switch (bootloader_src)
    {
        case 1: // SBEC3 (128k)
        {
            uint8_t bl_header[5] = { 0x4C, 0x01, 0x00, (((0x0100 + ARRAY_SIZE(LdBoot_128k_SBEC3) - 1) >> 8) & 0xFF), ((0x0100 + ARRAY_SIZE(LdBoot_128k_SBEC3) - 1) & 0xFF) };

            for (uint8_t i = 0; i < ARRAY_SIZE(bl_header); i++)
            {
                pcm_putc(bl_header[i]);
                while (pcm_rx_available() == 0); // wait for echo
                pcm_getc(); // read echo into oblivion
            }
            
            for (uint16_t i = 0; i < ARRAY_SIZE(LdBoot_128k_SBEC3); i++)
            {
                pcm_putc(pgm_read_byte(LdBoot_128k_SBEC3 + i));
                while (pcm_rx_available() == 0); // wait for echo
                pcm_getc(); // read echo into oblivion
            }
            break;
        }
        case 2: // SBEC3 (256k)
        {
            uint8_t bl_header[5] = { 0x4C, 0x01, 0x00, (((0x0100 + ARRAY_SIZE(LdBoot_256k_SBEC3) - 1) >> 8) & 0xFF), ((0x0100 + ARRAY_SIZE(LdBoot_256k_SBEC3) - 1) & 0xFF) };

            for (uint8_t i = 0; i < ARRAY_SIZE(bl_header); i++)
            {
                pcm_putc(bl_header[i]);
                while (pcm_rx_available() == 0); // wait for echo
                pcm_getc(); // read echo into oblivion
            }

            for (uint16_t i = 0; i < ARRAY_SIZE(LdBoot_256k_SBEC3); i++)
            {
                pcm_putc(pgm_read_byte(LdBoot_256k_SBEC3 + i));
                while (pcm_rx_available() == 0); // wait for echo
                pcm_getc(); // read echo into oblivion
            }
            break;
        }
        case 3: // SBEC3 256k custom by Dino
        {
            uint8_t bl_header[5] = { 0x4C, 0x01, 0x00, (((0x0100 + ARRAY_SIZE(LdBoot_256k_SBEC3_custom) - 1) >> 8) & 0xFF), ((0x0100 + ARRAY_SIZE(LdBoot_256k_SBEC3_custom) - 1) & 0xFF) };

            for (uint8_t i = 0; i < ARRAY_SIZE(bl_header); i++)
            {
                pcm_putc(bl_header[i]);
                while (pcm_rx_available() == 0); // wait for echo
                pcm_getc(); // read echo into oblivion
            }

            for (uint16_t i = 0; i < ARRAY_SIZE(LdBoot_256k_SBEC3_custom); i++)
            {
                pcm_putc(pgm_read_byte(LdBoot_256k_SBEC3_custom + i));
                while (pcm_rx_available() == 0); // wait for echo
                pcm_getc(); // read echo into oblivion
            }
            break;
        }
        case 0:
        default:
        {
            uint8_t bl_header[5] = { 0x4C, 0x01, 0x00, (((0x0100 + ARRAY_SIZE(LdBoot_empty_SBEC3) - 1) >> 8) & 0xFF), ((0x0100 + ARRAY_SIZE(LdBoot_empty_SBEC3) - 1) & 0xFF) };

            for (uint8_t i = 0; i < ARRAY_SIZE(bl_header); i++)
            {
                pcm_putc(bl_header[i]);
                while (pcm_rx_available() == 0); // wait for echo
                pcm_getc(); // read echo into oblivion
            }

            for (uint16_t i = 0; i < ARRAY_SIZE(LdBoot_empty_SBEC3); i++)
            {
                pcm_putc(pgm_read_byte(LdBoot_empty_SBEC3 + i));
                while (pcm_rx_available() == 0); // wait for echo
                pcm_getc(); // read echo into oblivion
            }
            break;
        }
    }

    wdt_reset(); // feed the watchdog
    pcm_rx_flush();

    uint8_t start_bootloader_cmd[3] = { 0x47, 0x01, 0x00 };

    // Write start bootloader message.
    for (uint8_t i = 0; i < ARRAY_SIZE(start_bootloader_cmd); i++)
    {
        pcm_putc(start_bootloader_cmd[i]);
        while (pcm_rx_available() == 0); // wait for echo
        pcm_getc(); // read echo into oblivion
    }

    while ((uint32_t)(millis() - pcm.last_byte_millis) < SCI_BTSTRP_DLY); // wait for response

    if (pcm_rx_available() == 0)
    {
        ret[0] = 7;
        send_usb_packet(bus_usb, debug, init_bootstrap_mode, ret, 1);
        pcm_rx_flush();
        return;
    }

    uint8_t bootloader_status = pcm_getc() & 0xFF;

    if (bootloader_status != 0x22)
    {
        ret[0] = 8;
        send_usb_packet(bus_usb, debug, init_bootstrap_mode, ret, 1);
        pcm_rx_flush();
        return;
    }

    wdt_reset(); // feed the watchdog
    pcm_rx_flush();

    // Success.
    send_usb_packet(bus_usb, debug, init_bootstrap_mode, ret, 1);
}

/*************************************************************************
Function: upload_worker_function()
Purpose:  upload worker function in bootstrap mode
**************************************************************************/
void write_worker_function(uint8_t worker_function_src)
{
    uint8_t ret[1] = { 0 };
    // 0 = ok
    // 1 = upload interrupted
    // 2 = unexpected upload result
    // 3 = function did not start
    // 4 = unexpected function start status

    wdt_reset(); // feed the watchdog
    pcm_rx_flush();
    
    switch (worker_function_src)
    {
        case 1: // part number read
        {
            uint8_t wf_header[3] = { 0x10, ((ARRAY_SIZE(LdPartNumberRead_SBEC3) >> 8) & 0xFF), (ARRAY_SIZE(LdPartNumberRead_SBEC3) & 0xFF) };

            for (uint8_t i = 0; i < ARRAY_SIZE(wf_header); i++)
            {
                pcm_putc(wf_header[i]);
                while (pcm_rx_available() == 0); // wait for echo
                pcm_getc(); // read echo into oblivion
            }

            for (uint16_t i = 0; i < ARRAY_SIZE(LdPartNumberRead_SBEC3); i++)
            {
                pcm_putc(pgm_read_byte(LdPartNumberRead_SBEC3 + i));
                while (pcm_rx_available() == 0); // wait for echo
                pcm_getc(); // read echo into oblivion
            }
            break;
        }
        case 2: // flash manufacturer and chip ID read
        {
            uint8_t wf_header[3] = { 0x10, ((ARRAY_SIZE(LdFlashID_SBEC3) >> 8) & 0xFF), (ARRAY_SIZE(LdFlashID_SBEC3) & 0xFF) };

            for (uint8_t i = 0; i < ARRAY_SIZE(wf_header); i++)
            {
                pcm_putc(wf_header[i]);
                while (pcm_rx_available() == 0); // wait for echo
                pcm_getc(); // read echo into oblivion
            }

            for (uint16_t i = 0; i < ARRAY_SIZE(LdFlashID_SBEC3); i++)
            {
                pcm_putc(pgm_read_byte(LdFlashID_SBEC3 + i));
                while (pcm_rx_available() == 0); // wait for echo
                pcm_getc(); // read echo into oblivion
            }
            break;
        }
        case 3: // flash read
        {
            uint8_t wf_header[3] = { 0x10, ((ARRAY_SIZE(LdFlashRead_SBEC3) >> 8) & 0xFF), (ARRAY_SIZE(LdFlashRead_SBEC3) & 0xFF) };

            for (uint8_t i = 0; i < ARRAY_SIZE(wf_header); i++)
            {
                pcm_putc(wf_header[i]);
                while (pcm_rx_available() == 0); // wait for echo
                pcm_getc(); // read echo into oblivion
            }

            for (uint16_t i = 0; i < ARRAY_SIZE(LdFlashRead_SBEC3); i++)
            {
                pcm_putc(pgm_read_byte(LdFlashRead_SBEC3 + i));
                while (pcm_rx_available() == 0); // wait for echo
                pcm_getc(); // read echo into oblivion
            }
            break;
        }
        case 7: // EEPROM read
        {
            uint8_t wf_header[3] = { 0x10, ((ARRAY_SIZE(LdEEPROMRead_SBEC3) >> 8) & 0xFF), (ARRAY_SIZE(LdEEPROMRead_SBEC3) & 0xFF) };

            for (uint8_t i = 0; i < ARRAY_SIZE(wf_header); i++)
            {
                pcm_putc(wf_header[i]);
                while (pcm_rx_available() == 0); // wait for echo
                pcm_getc(); // read echo into oblivion
            }

            for (uint16_t i = 0; i < ARRAY_SIZE(LdEEPROMRead_SBEC3); i++)
            {
                pcm_putc(pgm_read_byte(LdEEPROMRead_SBEC3 + i));
                while (pcm_rx_available() == 0); // wait for echo
                pcm_getc(); // read echo into oblivion
            }
            break;
        }
        case 8: // EEPROM write
        {
            uint8_t wf_header[3] = { 0x10, ((ARRAY_SIZE(LdEEPROMWrite_SBEC3) >> 8) & 0xFF), (ARRAY_SIZE(LdEEPROMWrite_SBEC3) & 0xFF) };

            for (uint8_t i = 0; i < ARRAY_SIZE(wf_header); i++)
            {
                pcm_putc(wf_header[i]);
                while (pcm_rx_available() == 0); // wait for echo
                pcm_getc(); // read echo into oblivion
            }

            for (uint16_t i = 0; i < ARRAY_SIZE(LdEEPROMWrite_SBEC3); i++)
            {
                pcm_putc(pgm_read_byte(LdEEPROMWrite_SBEC3 + i));
                while (pcm_rx_available() == 0); // wait for echo
                pcm_getc(); // read echo into oblivion
            }
            break;
        }
        case 0:
        default:
        {
            uint8_t wf_header[3] = { 0x10, ((ARRAY_SIZE(LdWorker_empty_SBEC3) >> 8) & 0xFF), (ARRAY_SIZE(LdWorker_empty_SBEC3) & 0xFF) };

            for (uint8_t i = 0; i < ARRAY_SIZE(wf_header); i++)
            {
                pcm_putc(wf_header[i]);
                while (pcm_rx_available() == 0); // wait for echo
                pcm_getc(); // read echo into oblivion
            }

            for (uint16_t i = 0; i < ARRAY_SIZE(LdWorker_empty_SBEC3); i++)
            {
                pcm_putc(pgm_read_byte(LdWorker_empty_SBEC3 + i));
                while (pcm_rx_available() == 0); // wait for echo
                pcm_getc(); // read echo into oblivion
            }
            break;
            break;
        }
    }

    // Wait for upload finished status byte.
    while ((uint32_t)(millis() - pcm.last_byte_millis) < SCI_BTSTRP_DLY); // wait for response

    if (pcm_rx_available() == 0)
    {
        ret[0] = 1;
        send_usb_packet(bus_usb, debug, upload_worker_function, ret, 1);
        pcm_rx_flush();
        return;
    }

    uint8_t upload_status = pcm_getc() & 0xFF;

    if (upload_status != 0x14)
    {
        ret[0] = 2;
        send_usb_packet(bus_usb, debug, upload_worker_function, ret, 1);
        pcm_rx_flush();
        return;
    }

//    wdt_reset(); // feed the watchdog
//    pcm_rx_flush();
//    pcm.last_byte_millis = millis();
//
//    // Start worker function.
//    pcm_putc(0x20);
//
//    while ((uint32_t)(millis() - pcm.last_byte_millis) < SCI_BTSTRP_DLY); // wait for response
//
//    if (pcm_rx_available() == 0)
//    {
//        ret[0] = 3;
//        send_usb_packet(bus_usb, debug, upload_worker_function, ret, 1);
//        pcm_rx_flush();
//        return;
//    }
//
//    uint8_t start_status = pcm_getc() & 0xFF;
//
//    if (start_status != 0x21)
//    {
//        ret[0] = 4;
//        send_usb_packet(bus_usb, debug, upload_worker_function, ret, 1);
//        pcm_rx_flush();
//        return;
//    }

    wdt_reset(); // feed the watchdog
    pcm_rx_flush();

    // Success.
    send_usb_packet(bus_usb, debug, upload_worker_function, ret, 1);
}

/*************************************************************************
Function: restore_pcm_eeprom_handler()
Purpose:  read current PCM EEPROM value and replace with backup value if different
**************************************************************************/
void restore_pcm_eeprom_handler(uint8_t *input_data)
{
    uint8_t ret[1] = { 0 };
    // 0 = ok
    // 1 = no response to security seed request
    // 2 = checksum error
    // 3 = no response to key
    // 4 = key not accepted
    // 5 = read EEPROM command not returning a value
    // 6 = write EEPROM command not returning a result
    // 7 = write EEPROM command failed

    wdt_reset(); // feed the watchdog
    pcm_rx_flush();
    pcm_tx_flush();
    pcm.last_byte_millis = millis();

    // Get security seed challenge.
    pcm_putc(0x2B);

    while ((pcm_rx_available() < 4) && ((uint32_t)(millis() - pcm.last_byte_millis) < 200)); // wait for response

    if (pcm_rx_available() < 4)
    {
        ret[0] = 1;
        send_usb_packet(bus_usb, debug, restore_pcm_eeprom, ret, 1);
        pcm_rx_flush();
        return;
    }

    uint8_t buff[16];
    uint8_t buff_ptr = 0;
    uint8_t checksum = 0;

    for (uint8_t i = 0; i < 4; i++)
    {
        buff[i] = pcm_getc() & 0xFF;

        if (i < 3) checksum += buff[i]; // calculate checksum
    }

    if (buff[3] != checksum)
    {
        ret[0] = 2;
        send_usb_packet(bus_usb, debug, restore_pcm_eeprom, ret, 1);
        pcm_rx_flush();
        return;
    }

    send_usb_packet(bus_pcm, msg_rx, sci_ls_bytes, buff, 4);

    bool key_required = true;

    if ((buff[1] == 0) && (buff[2] == 0))
    {
        key_required = false;
    }

    if (key_required)
    {
        uint16_t seed = to_uint16(buff[1], buff[2]);
        uint16_t a = (seed << 2) + 0x9018;
        uint8_t key[2] = { ((a >> 8) & 0xFF), (a & 0xFF) };

        uint8_t send_key_cmd[4] = { 0x2C, key[0], key[1], 0 };
        send_key_cmd[3] = calculate_checksum(send_key_cmd, 0, ARRAY_SIZE(send_key_cmd) - 1);

        wdt_reset(); // feed the watchdog
        pcm_rx_flush();
        buff_ptr = 0;

        // Write security key message.
        for (uint8_t i = 0; i < ARRAY_SIZE(send_key_cmd); i++)
        {
            pcm_putc(send_key_cmd[i]);
            while (pcm_rx_available() == 0); // wait for echo
            buff[i] = pcm_getc() & 0xFF; // read echo into buffer
            buff_ptr++;
        }

        while ((pcm_rx_available() == 0) && (uint32_t)(millis() - pcm.last_byte_millis) < 200); // wait for response

        if (pcm_rx_available() == 0)
        {
            ret[0] = 3;
            send_usb_packet(bus_usb, debug, restore_pcm_eeprom, ret, 1);
            pcm_rx_flush();
            return;
        }

        // Read key status.
        buff[buff_ptr] = pcm_getc() & 0xFF;
        buff_ptr++;

        send_usb_packet(bus_pcm, msg_rx, sci_ls_bytes, buff, buff_ptr);

        if (buff[4] != 0)
        {
            ret[0] = 4;
            send_usb_packet(bus_usb, debug, restore_pcm_eeprom, ret, 1);
            pcm_rx_flush();
            return;
        }
    }

    wdt_reset(); // feed the watchdog
    pcm_rx_flush();

    uint8_t read_eeprom_cmd[3] = { 0x28, 0x00, 0x00 };
    uint8_t write_eeprom_cmd[4] = { 0x27, 0x00, 0x00, 0x00 };
    uint8_t offset[2] = { 0, 0 };
    uint8_t attempts = 0;
    bool valid_response = false;

    for (uint16_t i = 0; i < 512; i++) // EEPROM size = 512 bytes
    {
        // Set current offset.
        offset[0] = (i >> 8) & 0xFF;
        offset[1] = i & 0xFF;
        read_eeprom_cmd[1] = offset[0];
        read_eeprom_cmd[2] = offset[1];

        valid_response = false;
        attempts = 0;

        while (!valid_response)
        {
            wdt_reset(); // feed the watchdog
            pcm_rx_flush();
            buff_ptr = 0;

            // Read current EEPROM value.
            for (uint8_t j = 0; j < ARRAY_SIZE(read_eeprom_cmd); j++)
            {
                pcm_putc(read_eeprom_cmd[j]);
                while (pcm_rx_available() == 0); // wait for echo
                buff[j] = pcm_getc() & 0xFF; // read echo into buffer
                buff_ptr++;
            }

            while ((pcm_rx_available() == 0) && ((uint32_t)(millis() - pcm.last_byte_millis) < 300)); // wait for response

            if (pcm_rx_available() == 0)
            {
                attempts++;

                if (attempts >= 10)
                {
                    ret[0] = 5;
                    send_usb_packet(bus_usb, debug, restore_pcm_eeprom, ret, 1);
                    pcm_rx_flush();
                    return;
                }

                delay(100);
            }
            else
            {
                valid_response = true;
            }
        }

        buff[buff_ptr] = pcm_getc() & 0xFF; // read response (current EEPROM byte)
        buff_ptr++;
        
        send_usb_packet(bus_pcm, msg_rx, sci_ls_bytes, buff, buff_ptr);

        // Update EEPROM byte if different.
        if (input_data[i] != buff[3])
        {
            write_eeprom_cmd[1] = offset[0];
            write_eeprom_cmd[2] = offset[1];
            write_eeprom_cmd[3] = input_data[i];

            valid_response = false;
            attempts = 0;

            while (!valid_response)
            {
                wdt_reset(); // feed the watchdog
                pcm_rx_flush();
                buff_ptr = 0;

                // Write new EEPROM value.
                for (uint8_t j = 0; j < ARRAY_SIZE(write_eeprom_cmd); j++)
                {
                    pcm_putc(write_eeprom_cmd[j]);
                    while (pcm_rx_available() == 0); // wait for echo
                    buff[j] = pcm_getc() & 0xFF; // read echo into buffer
                    buff_ptr++;
                }

                while ((pcm_rx_available() == 0) && ((uint32_t)(millis() - pcm.last_byte_millis) < 300)); // wait for response

                if (pcm_rx_available() == 0)
                {
                    attempts++;

                    if (attempts >= 10)
                    {
                        ret[0] = 6;
                        send_usb_packet(bus_usb, debug, restore_pcm_eeprom, ret, 1);
                        pcm_rx_flush();
                        return;
                    }

                    delay(100);
                }
                else
                {
                    buff[buff_ptr] = pcm_getc() & 0xFF;
                    buff_ptr++;
                    send_usb_packet(bus_pcm, msg_rx, sci_ls_bytes, buff, buff_ptr);

                    if (buff[4] == 0xE2) // EEPROM write successful
                    {
                        valid_response = true;
                    }
                    else
                    {
                        attempts++;

                        if (attempts >= 10)
                        {
                            ret[0] = 7;
                            send_usb_packet(bus_usb, debug, restore_pcm_eeprom, ret, 1);
                            pcm_rx_flush();
                            return;
                        }
    
                        delay(100);
                    }
                }
            }
        }

        handle_leds();
    }

    wdt_reset(); // feed the watchdog
    pcm_rx_flush();

    // Success.
    send_usb_packet(bus_usb, debug, restore_pcm_eeprom, ret, 1);
}

/*************************************************************************
Function: eep_init()
Purpose:  initialize external EEPROM
**************************************************************************/
void eep_init(void)
{
    eep_status = eep.begin(extEEPROM::twiClock400kHz);

    if (eep_status) // non-zero = bad
    { 
        eep_present = false;
        send_usb_packet(bus_usb, ok_error, error_eep_not_found, err, 1);
    }
    else // zero = good
    {
        eep_present = true;
    }
}

/*************************************************************************
Function: write_default_settings()
Purpose:  write default settings to internal EEPROM
**************************************************************************/
void write_default_settings(void)
{
    // Memory map:
    // $00-$01: hardware version (multiplied by 100, example: V1.40 = 140(DEC) = $008C; V1.41 = 141(DEC) = $008D; V1.42 = 142(DEC) = $008E; V1.43 = 143(DEC) = $008F)
    // $02-$09: hardware date (PCB order date, 64-bit UNIX time)
    // $0A-$11: assembly date (Scanner assembly date, 64-bit UNIX time)
    // $12-$13: ADC supply voltage multiplied by 100 (example 5.00V = 500(DEC) = $01F4)
    // $14-$15: high resistor value in the voltage divider: 27 kOhm = 27000(DEC) = $6978
    // $16-$17: low resistor value in the voltage divider: 5.1 kOhm = 5100(DEC) = $13EC
    // $18:     LCD enabled/disabled
    // $19:     LCD I2C address
    // $1A:     LCD column size
    // $1B:     LCD row size
    // $1C:     LCD refresh rate (Hz)
    // $1D:     LCD imperial/metric units (0: imperial, 1: metric)
    // $1E:     LCD data source (1: CCD-bus, 2: SCI-bus (PCM), 3: SCI-bus (TCM))
    // $1F-$20: LED heartbeat interval (5000 ms)
    // $21-$22: LED blink duration (50 ms)
    // $23:     CCD-bus settings
    // $24:     SCI-bus (PCM) settings
    // $25:     SCI-bus (TCM) settings
    // $26:     CCD-bus automatic request messages
    // $27:     SCI-bus (PCM) automatic request messages
    // $28:     SCI-bus (TCM) automatic request messages
    // $29-$FE: reserved for future data

    uint8_t default_settings[41] =
    { //  00    01    02    03    04    05    06    07    08    09    0A    0B    0C    0D    0E    0F
        0x00, 0x96, 0x00, 0x00, 0x00, 0x00, 0x61, 0xF9, 0x08, 0x37, 0x00, 0x00, 0x00, 0x00, 0x61, 0xF9, // 00
        0x08, 0x37, 0x01, 0xF4, 0x69, 0x78, 0x13, 0xEC, 0x00, 0x27, 0x14, 0x04, 0x14, 0x00, 0x01, 0x13, // 10
        0x88, 0x00, 0x32, 0x41, 0x91, 0xC1, 0x00, 0x00, 0x00                                            // 20
    };

    for (uint16_t i = 0; i < 41; i++)
    {
        EEPROM.update(i, default_settings[i]);
    }
}

/*************************************************************************
Function: load_settings()
Purpose:  load settings from ATmega2560's internal EEPROM (V1.50+)
          or copy settings from external EEPROM (V1.40 - V1.44)
**************************************************************************/
void load_settings(void)
{
    if (((EEPROM.read(0) == 0x00) && (EEPROM.read(1) == 0x00)) || (EEPROM.read(0) == 0xFF)) // V1.40 - V1.44, copy settings from external to internal EEPROM
    {
        if (eep_present)
        {
            if (eep.read(0) != 0xFF) // settings are present in external EEPROM
            {
                for (uint16_t i = 0; i < 41; i++) // copy first 41 bytes to internal EEPROM
                {
                    EEPROM.update(i, eep.read(i));
                }
            }
            else // external EEPROM is empty
            {
                write_default_settings();
            }
        }
        else // external EEPROM is missing
        {
            write_default_settings();
        }
    }

    // Load and apply settings.

    uint8_t data[2] = { 0x00, 0x00 };

    hw_version[0] = EEPROM.read(0x00);
    hw_version[1] = EEPROM.read(0x01);

    if (to_uint16(hw_version[0], hw_version[1]) < 150)
    {
        eep = extEEPROM(kbits_32, 1, 32, 0x50); // device size: 32 kilobits = 4 kilobytes, number of devices: 1, page size: 32 bytes (from datasheet), device address: 0x50 by default
        eep.begin(extEEPROM::twiClock400kHz);
    }
    else
    {
        eep = extEEPROM(kbits_512, 1, 128, 0x50); // device size: 512 kilobits = 64 kilobytes, number of devices: 1, page size: 128 bytes (from datasheet), device address: 0x50 by default
        eep.begin(extEEPROM::twiClock400kHz);
    }

    hw_date[0] = EEPROM.read(0x02);
    hw_date[1] = EEPROM.read(0x03);
    hw_date[2] = EEPROM.read(0x04);
    hw_date[3] = EEPROM.read(0x05);
    hw_date[4] = EEPROM.read(0x06);
    hw_date[5] = EEPROM.read(0x07);
    hw_date[6] = EEPROM.read(0x08);
    hw_date[7] = EEPROM.read(0x09);

    assembly_date[0] = EEPROM.read(0x0A);
    assembly_date[1] = EEPROM.read(0x0B);
    assembly_date[2] = EEPROM.read(0x0C);
    assembly_date[3] = EEPROM.read(0x0D);
    assembly_date[4] = EEPROM.read(0x0E);
    assembly_date[5] = EEPROM.read(0x0F);
    assembly_date[6] = EEPROM.read(0x10);
    assembly_date[7] = EEPROM.read(0x11);

    data[0] = EEPROM.read(0x12);
    data[1] = EEPROM.read(0x13);
    adc_supply_voltage = to_uint16(data[0], data[1]);

    data[0] = EEPROM.read(0x14);
    data[1] = EEPROM.read(0x15);
    rd_high_value = to_uint16(data[0], data[1]);

    data[0] = EEPROM.read(0x16);
    data[1] = EEPROM.read(0x17);
    rd_low_value = to_uint16(data[0], data[1]);

    EEPROM.read(0x18) ? (lcd_enabled = true) : (lcd_enabled = false);

    lcd_i2c_address = EEPROM.read(0x19);
    lcd_char_width = EEPROM.read(0x1A);
    lcd_char_height = EEPROM.read(0x1B);
    lcd_refresh_rate = EEPROM.read(0x1C);
    lcd_update_interval = 1000 / lcd_refresh_rate;
    lcd_units = EEPROM.read(0x1D);
    lcd_data_source = EEPROM.read(0x1E);

    data[0] = EEPROM.read(0x1F);
    data[1] = EEPROM.read(0x20);
    heartbeat_interval = to_uint16(data[0], data[1]);
    heartbeat_interval ? (heartbeat_enabled = true) : (heartbeat_enabled = false);

    data[0] = EEPROM.read(0x21);
    data[1] = EEPROM.read(0x22);
    led_blink_duration = to_uint16(data[0], data[1]);

    ccd.bus_settings = EEPROM.read(0x23);
    if (ccd.bus_settings == 0x00) ccd.bus_settings = 0xC1;
    configure_ccd_bus(ccd.bus_settings);

    pcm.bus_settings = EEPROM.read(0x24);
    if (pcm.bus_settings == 0x00) pcm.bus_settings = 0x81;

    tcm.bus_settings = EEPROM.read(0x25);
    if (tcm.bus_settings == 0x00) tcm.bus_settings = 0x21;

    ccd.auto_request = EEPROM.read(0x26);

    if (ccd.auto_request == 0xFF)
    {
        ccd.auto_request = 0;
        EEPROM.update(0x26, ccd.auto_request);
    }

    pcm.auto_request = EEPROM.read(0x27);

    if (pcm.auto_request == 0xFF)
    {
        pcm.auto_request = 0;
        EEPROM.update(0x27, pcm.auto_request);
    }
    
    tcm.auto_request = EEPROM.read(0x28);

    if (tcm.auto_request == 0xFF)
    {
        tcm.auto_request = 0;
        EEPROM.update(0x28, tcm.auto_request);
    }
}

/*************************************************************************
Function: lcd_init()
Purpose:  initialize LCD
**************************************************************************/
void lcd_init(void)
{
    lcd_splash_screen_on = true;
    lcd = LiquidCrystal_I2C(lcd_i2c_address, lcd_char_width, lcd_char_height);
    lcd.begin();
    lcd.backlight(); // backlight on
    lcd.clear(); // clear display
    lcd.home(); // set cursor in home position (0, 0)
    float hw_ver = to_uint16(hw_version[0], hw_version[1]) / 100.0;
        
    if ((lcd_char_width == 20) && (lcd_char_height == 4)) // 20x4 LCD
    {
        lcd.print(F("--------------------")); // F(" ") makes the compiler store the string inside flash memory instead of RAM, good practice if system is low on RAM
        lcd.setCursor(0, 1);
        lcd.print(F("  CHRYSLER CCD/SCI  "));
        lcd.setCursor(0, 2);
        lcd.print(F("   SCANNER V"));
        lcd.print(hw_ver, 2);
        lcd.print(F("    "));
        lcd.setCursor(0, 3);
        lcd.print(F("--------------------"));
    }
    else if ((lcd_char_width == 16) && (lcd_char_height == 2)) // 16x2 LCD
    {
        lcd.print(F("CHRYSLER CCD/SCI")); // F(" ") makes the compiler store the string inside flash memory instead of RAM, good practice if system is low on RAM
        lcd.setCursor(0, 1);
        lcd.print(F(" SCANNER V"));
        lcd.print(hw_ver, 2);
        lcd.print(F("  "));
    }
    else
    {
        lcd.print(F("CCD/SCI"));
    }

    lcd.createChar(0, up_symbol); // custom character from "upsymbol" variable with id number 0
    lcd.createChar(1, down_symbol);
    lcd.createChar(2, left_symbol);
    lcd.createChar(3, right_symbol);
    lcd.createChar(4, enter_symbol);
    lcd.createChar(5, degree_symbol);
}

/*************************************************************************
Function: print_display_layout_1_metric()
Purpose:  printing default metric display layout to LCD (km/h, km...)
Note:     prints when switching between different layouts
**************************************************************************/
void print_display_layout_1_metric(void)
{
    lcd.clear();
    
    if ((lcd_char_width == 20) && (lcd_char_height == 4)) // 20x4 LCD
    {
        lcd.setCursor(0, 0);
        lcd.print(F("  0km/h    0rpm     ")); // 1st line
        lcd.setCursor(0, 1);
        lcd.print(F("  0/  0 C     0.0kPa")); // 2nd line 
        lcd.setCursor(0, 2);
        lcd.print(F(" 0.0/ 0.0V    0.000V")); // 3rd line
        lcd.setCursor(0, 3);
        lcd.print(F("     0.000km    0kPa")); // 4th line
        lcd.setCursor(7, 1);
        lcd.write((uint8_t)5); // print degree symbol
    }
    else if ((lcd_char_width == 16) && (lcd_char_height == 2)) // 16x2 LCD
    {
        lcd.setCursor(0, 0);
        lcd.print(F("  0km/h     0rpm")); // 1st line
        lcd.setCursor(0, 1);
        lcd.print(F("  0 C     0.0kPa")); // 2nd line 
        lcd.setCursor(3, 1);
        lcd.write((uint8_t)5); // print degree symbol
    }
    else
    {
        lcd.setCursor(0, 0);
        lcd.print(F("    0rpm")); // 1st line
    }
}

/*************************************************************************
Function: print_display_layout_1_imperial()
Purpose:  printing default metric display layout to LCD (mph, mi...)
Note:     prints when switching between different layouts
**************************************************************************/
void print_display_layout_1_imperial(void)
{
    lcd.clear();
    
    if ((lcd_char_width == 20) && (lcd_char_height == 4)) // 20x4 LCD
    {
        lcd.setCursor(0, 0);
        lcd.print(F("  0mph     0rpm     ")); // 1st line
        lcd.setCursor(0, 1);
        lcd.print(F("  0/  0 F     0.0psi")); // 2nd line 
        lcd.setCursor(0, 2);
        lcd.print(F(" 0.0/ 0.0V    0.000V")); // 3rd line
        lcd.setCursor(0, 3);
        lcd.print(F("     0.000mi    0psi")); // 4th line
        lcd.setCursor(7, 1);
        lcd.write((uint8_t)5); // print degree symbol
    }
    else if ((lcd_char_width == 16) && (lcd_char_height == 2)) // 16x2 LCD
    {
        lcd.setCursor(0, 0);
        lcd.print(F("  0mph      0rpm")); // 1st line
        lcd.setCursor(0, 1);
        lcd.print(F("  0 F     0.0psi")); // 2nd line 
        lcd.setCursor(3, 1);
        lcd.write((uint8_t)5); // print degree symbol
    }
    else
    {
        lcd.setCursor(0, 0);
        lcd.print(F("    0rpm")); // 1st line
    }
}

/*************************************************************************
Function: handle_lcd()
Purpose:  write stuff to LCD
Note:     uncomment cases when necessary
**************************************************************************/
void handle_lcd(uint8_t bus, uint8_t *data, uint8_t index, uint8_t datalength)
{
    if (lcd_enabled)
    {
//        current_millis = millis(); // check current time
//        if ((uint32_t)(current_millis - lcd_last_update ) >= lcd_update_interval) // refresh rate
//        {
//            lcd_last_update = current_millis;
            
            uint8_t message_length = datalength-index;
            uint8_t message[message_length];

            if (message_length == 0) return;
        
            for (uint8_t i = index; i < datalength; i++)
            {
                message[i-index] = data[i]; // make a local copy of the source array
            }

            switch (lcd_data_source)
            {
                case bus_ccd:
                {
                    if (bus == bus_ccd)
                    {
                        switch (message[0]) // check ID-byte
                        {
                            case 0x24: // VEHICLE SPEED
                            {
                                if (message_length > 3)
                                {
                                    uint8_t vehicle_speed = 0;
                                    
                                    if (lcd_units == 0) // imperial
                                    {
                                        vehicle_speed = message[1];
                                    }
                                    else if (lcd_units == 1) // metric
                                    {
                                        vehicle_speed = message[2];
                                    }
        
                                    if (((lcd_char_width == 20) && (lcd_char_height == 4)) || ((lcd_char_width == 16) && (lcd_char_height == 2))) // 20x4 / 16x2 LCD
                                    {
                                        if (vehicle_speed < 10)
                                        {
                                            lcd.setCursor(0, 0);
                                            lcd.print("  ");
                                            lcd.print(vehicle_speed);
                                        }
                                        else if ((vehicle_speed >= 10) && (vehicle_speed < 100))
                                        {
                                            lcd.setCursor(0, 0);
                                            lcd.print(" ");
                                            lcd.print(vehicle_speed);
                                        }
                                        else if (vehicle_speed >= 100)
                                        {
                                            lcd.setCursor(0, 0);
                                            lcd.print(vehicle_speed);
                                        }
                                    }
                                    else
                                    {
                                        
                                    }
                                }
                                break;
                            }
                            case 0x42: // THROTTLE POSITION SENSOR | CRUISE CONTROL
                            {
                                if (message_length > 3)
                                {
                                    float tps_delta_voltage = roundf(message[1] * 1000.0 * 0.0196);
                                    tps_delta_voltage = tps_delta_voltage / 1000.0;

                                    if ((lcd_char_width == 20) && (lcd_char_height == 4)) // 20x4 LCD
                                    {
                                        lcd.setCursor(14, 2);
                                        lcd.print(tps_delta_voltage, 3);
                                    }
                                    else if ((lcd_char_width == 16) && (lcd_char_height == 2)) // 16x2 LCD
                                    {
                                        
                                    }
                                    else
                                    {
                                        
                                    }
                                }
                                break;
                            }
                            case 0x8C: // ENGINE COOLANT TEMPERATURE | INTAKE AIR TEMPERATURE
                            {
                                if (message_length > 3)
                                {
                                    int coolant_temp = 0;
                                    int intake_temp = 0;
                                    
                                    if (lcd_units == 0) // imperial
                                    {
                                        coolant_temp = round((message[1] * 1.8) - 198.4);
                                        intake_temp = round((message[2] * 1.8) - 198.4);
                                    }
                                    else if (lcd_units == 1) // metric
                                    {
                                        coolant_temp = message[1] - 128;
                                        intake_temp = message[2] - 128;
                                    }
        
                                    if ((lcd_char_width == 20) && (lcd_char_height == 4)) // 20x4 LCD
                                    {
                                        if (coolant_temp <= -100)
                                        {
                                            lcd.setCursor(0, 1);
                                            lcd.print("-99");
                                        }
                                        else if ((coolant_temp > -100) && (coolant_temp <= -10))
                                        {
                                            lcd.setCursor(0, 1);
                                            lcd.print(coolant_temp);
                                        }
                                        else if ((coolant_temp > -10) && (coolant_temp < 0))
                                        {
                                            lcd.setCursor(0, 1);
                                            lcd.print(" ");
                                            lcd.print(coolant_temp);
                                        }
                                        else if ((coolant_temp >= 0) && (coolant_temp < 10))
                                        {
                                            lcd.setCursor(0, 1);
                                            lcd.print("  ");
                                            lcd.print(coolant_temp);
                                        }
                                        else if ((coolant_temp >= 10) && (coolant_temp < 100))
                                        {
                                            lcd.setCursor(0, 1);
                                            lcd.print(" ");
                                            lcd.print(coolant_temp);
                                        }
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
                                        {
                                            lcd.setCursor(0, 1);
                                            lcd.print(coolant_temp);
                                        }
                                    }
                                    else
                                    {
                                        
                                    }
                                }
                                break;
                            }
                            case 0x0C: // ENGINE COOLANT TEMPERATURE | INTAKE AIR TEMPERATURE + BATTERY VOLTAGE + OIL PRESSURE
                            {
                                if (message_length > 3)
                                {
                                    uint16_t oil_pressure;

                                    if (lcd_units == 0) // imperial
                                    {
                                        oil_pressure = round(message[2] * 0.5);
                                    }
                                    else if (lcd_units == 1) // metric
                                    {
                                        oil_pressure = round(message[2] * 6.894757 * 0.5);
                                    }
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
void loop()
{
    wdt_reset(); // reset watchdog timer to 0 seconds so no accidental restart occurs
    handle_usb_data(); // look for commands over USB connection
    handle_ccd_data(); // do CCD-bus stuff
    handle_sci_data(); // do SCI-bus stuff
    handle_leds(); // do LED stuff
}
